reivaxy/celloAid/shell_3/20241109_110924.jpg

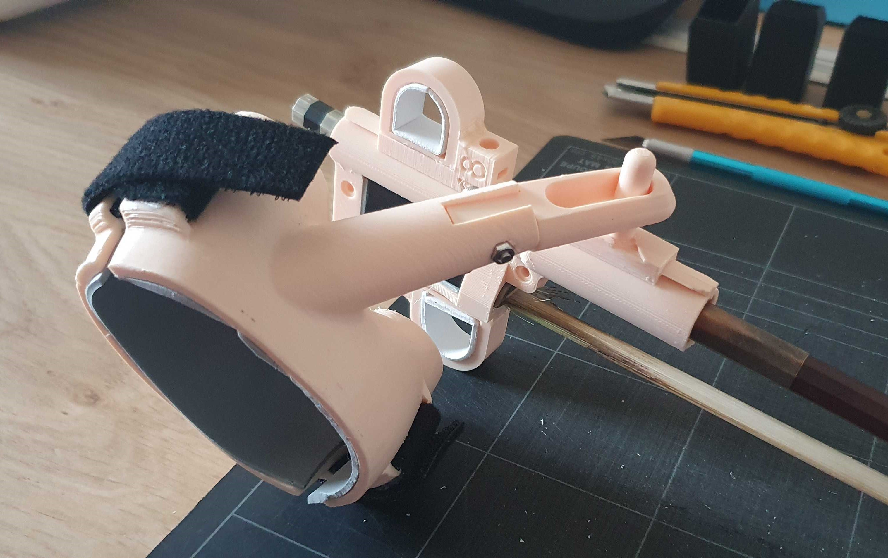
shell_3/20241109_110924.jpg
