reivaxy/celloAid/shell_3/20241109_110940.jpg

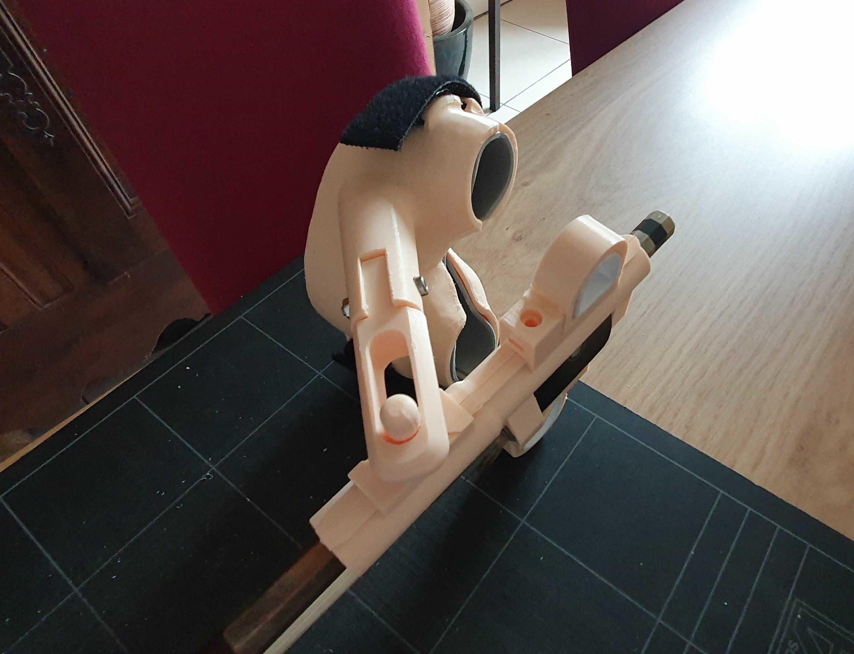
shell_3/20241109_110940.jpg
