reivaxy/celloAid/shell_3/20241109_110947.jpg

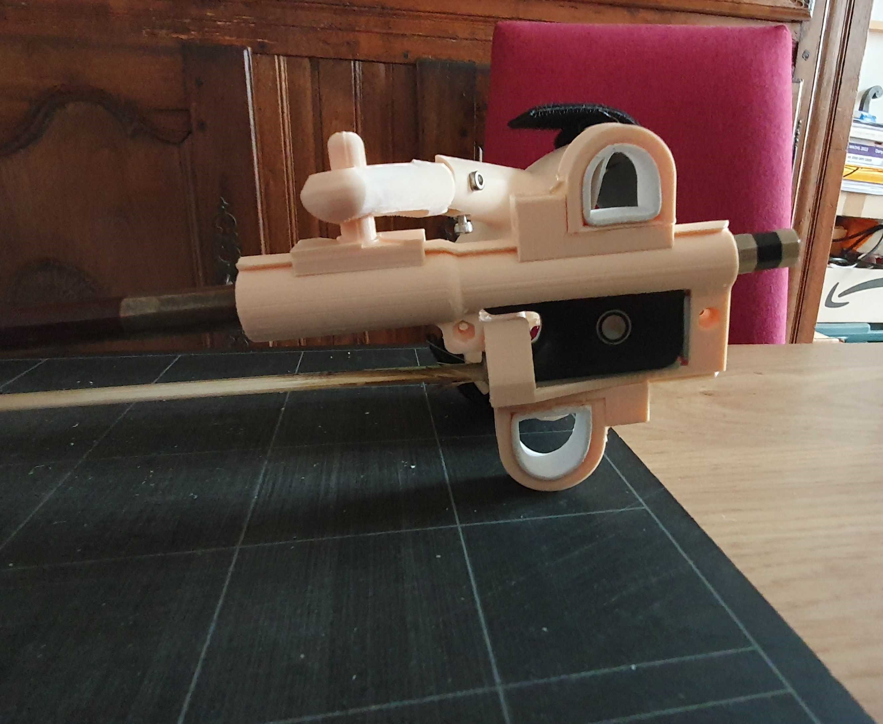
shell_3/20241109_110947.jpg
