reivaxy/celloAid/shell_3/index.stl

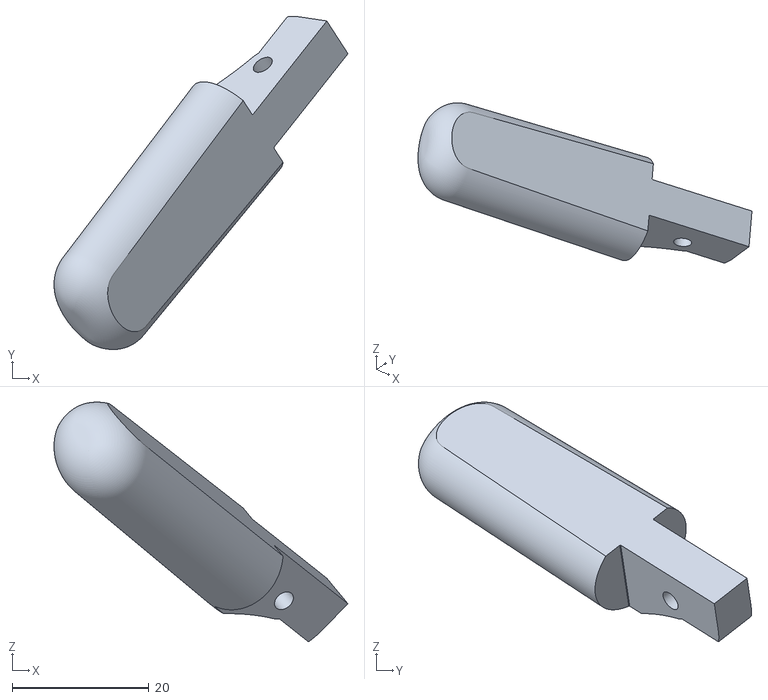
[picture p26: CAD file, 2024-11-09]
shell_3/index.stl
42.9 x 48.6 x 35.0
