reivaxy/celloAid/bow_1/hinge v2.stl

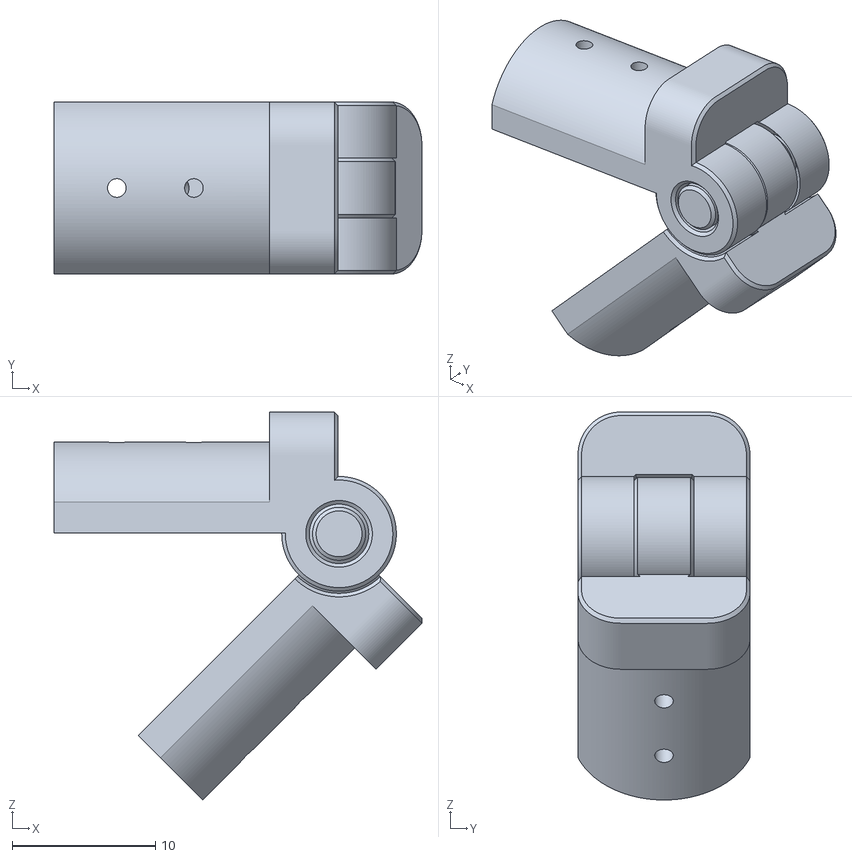
[picture p27: CAD file, 2024-08-30]
bow_1/hinge v2.stl
25.7 x 12.0 x 27.1
