reivaxy/celloAid/bow_2/lock.stl

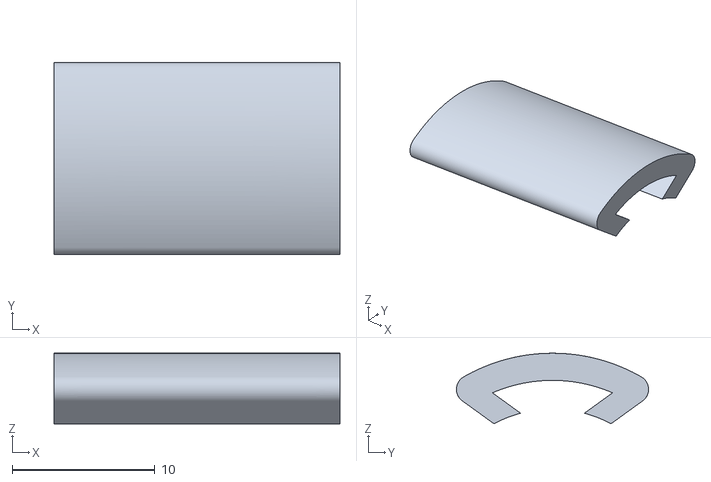
[picture p28: CAD file, 2024-08-30]
bow_2/lock.stl
20.0 x 13.4 x 4.93
