reivaxy/celloAid/bow_3/finger/circles/fingerRing.3mf

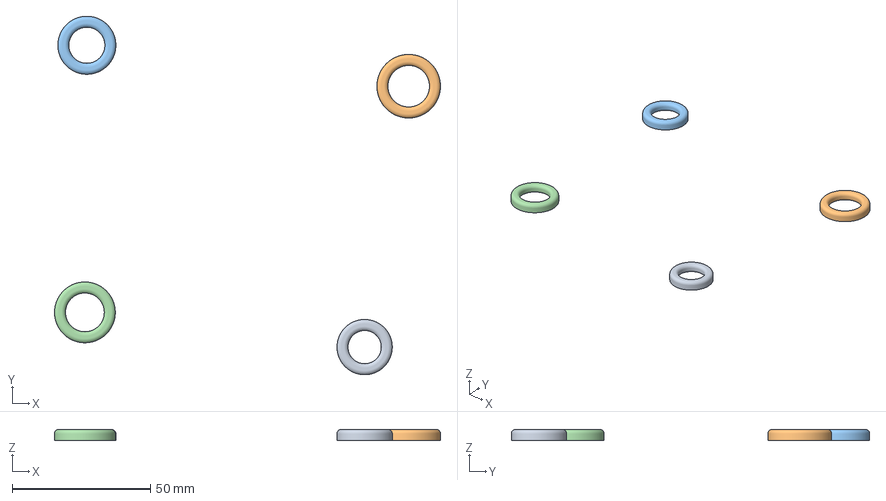
[picture p29: CAD file, 2024-09-11]
bow_3/finger/circles/fingerRing.3mf
139.6 x 129.7 x 4.00 mm
fingerRing12.stl
fingerRing15.stl
fingerRing13.stl
fingerRing14.stl
