reivaxy/celloAid/bow_3/finger/fingerSlider12.3mf

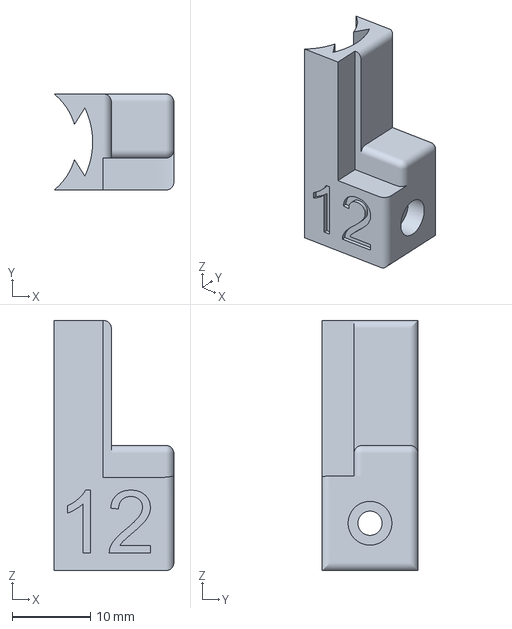
[picture p30: CAD file, 2024-10-21]
bow_3/finger/fingerSlider12.3mf
15.3 x 12.3 x 32.0 mm
