reivaxy/celloAid/bow_3/thumb/circles/thumbSlider20.3mf

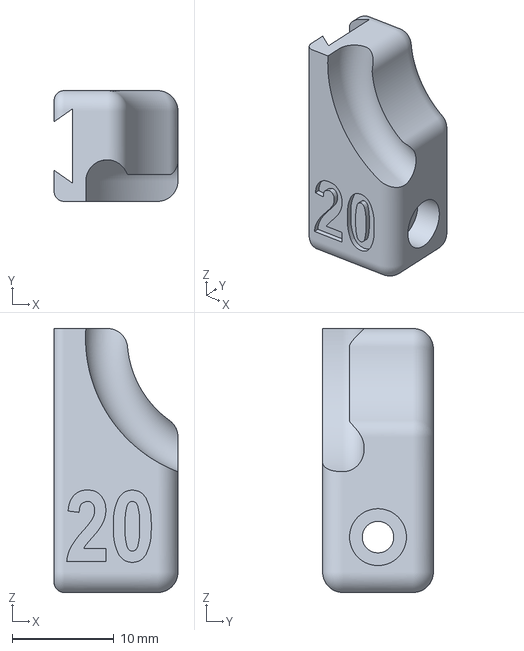
[picture p31: CAD file, 2024-09-11]
bow_3/thumb/circles/thumbSlider20.3mf
12.2 x 10.9 x 26.0 mm
