reivaxy/celloAid/bow_3/thumb/thumbRing16.3mf

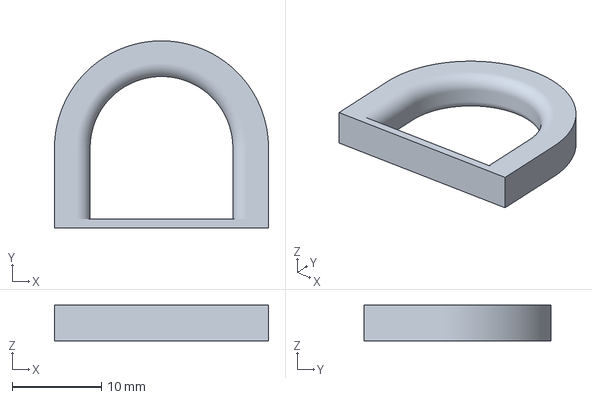
[picture p32: CAD file, 2024-10-21]
bow_3/thumb/thumbRing16.3mf
24.0 x 21.0 x 4.00 mm
