reivaxy/celloAid/bow_3/tubeRight.stl

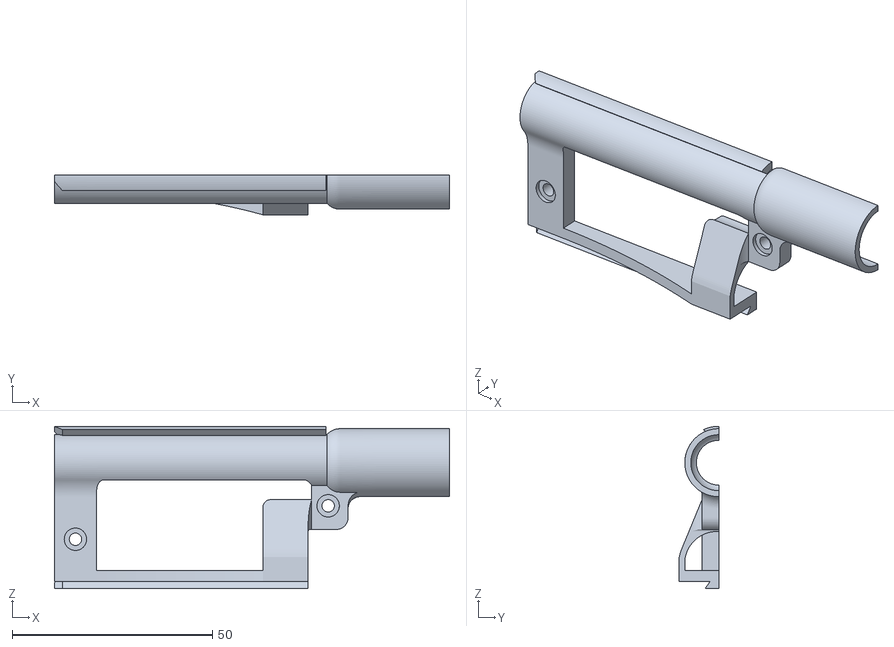
[picture p33: CAD file, 2024-08-30]
bow_3/tubeRight.stl
98.7 x 9.90 x 40.6
