reivaxy/celloAid/bow_4/indexRing5.stl

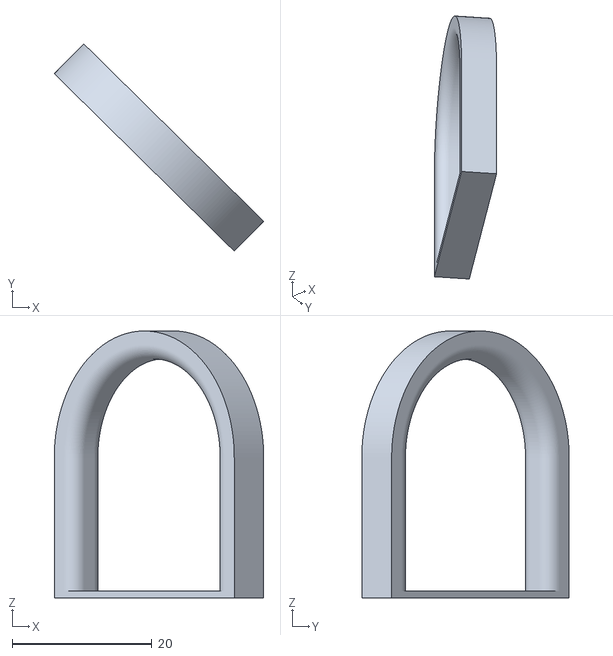
[picture p34: CAD file, 2024-11-09]
bow_4/indexRing5.stl
30.0 x 29.7 x 38.2
