reivaxy/celloAid/bow_5/bowBackHollower.stl

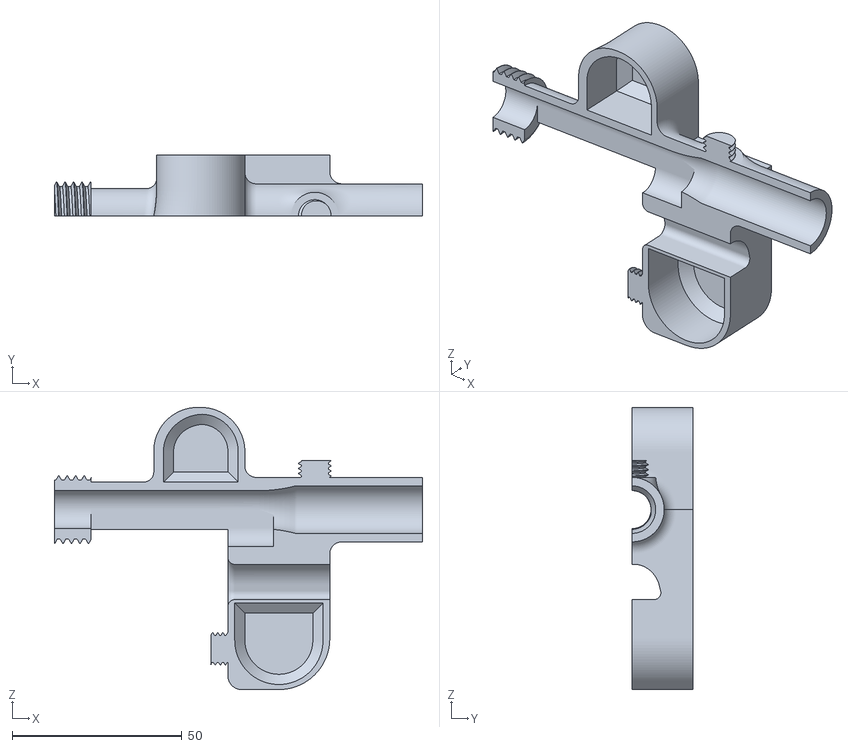
[picture p35: CAD file, 2024-11-27]
bow_5/bowBackHollower.stl
108.4 x 18.0 x 83.1
