reivaxy/celloAid/bow_7/front.stl

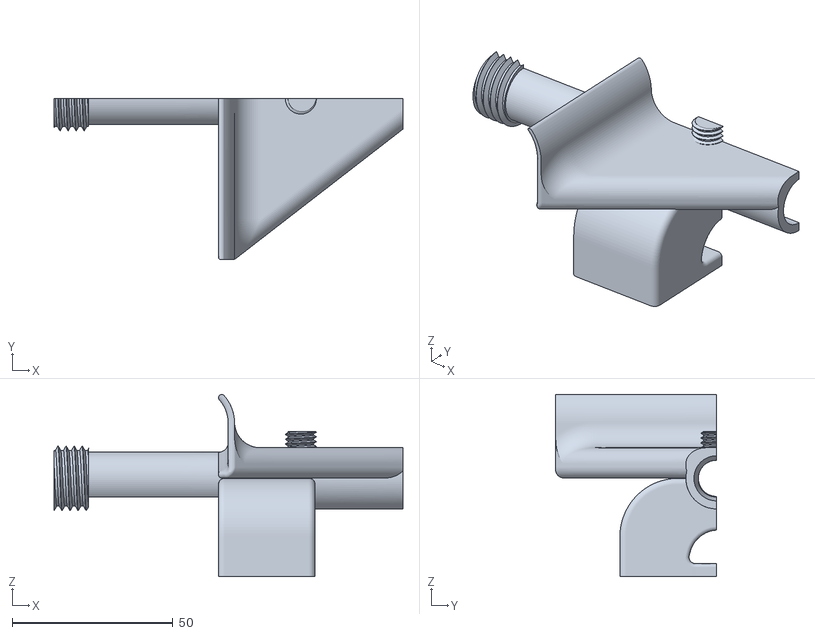
[picture p36: CAD file, 2025-01-11]
bow_7/front.stl
108.4 x 50.0 x 56.5
