reivaxy/celloAid/shell_1/tpuHinge.stl

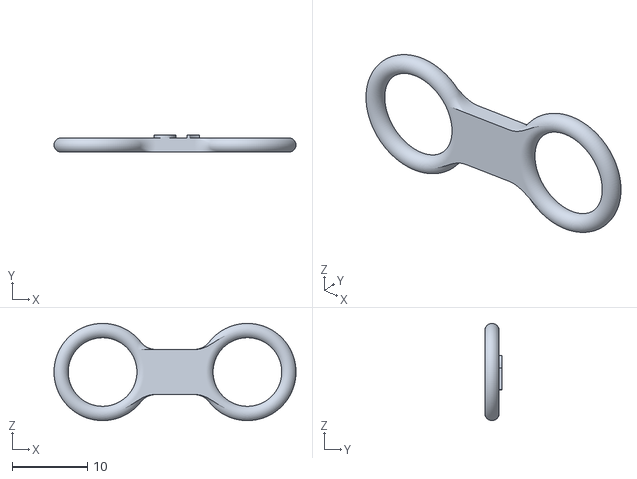
[picture p37: CAD file, 2024-08-30]
shell_1/tpuHinge.stl
32.1 x 2.30 x 12.9
