reivaxy/celloAid/shell_2/top.3mf

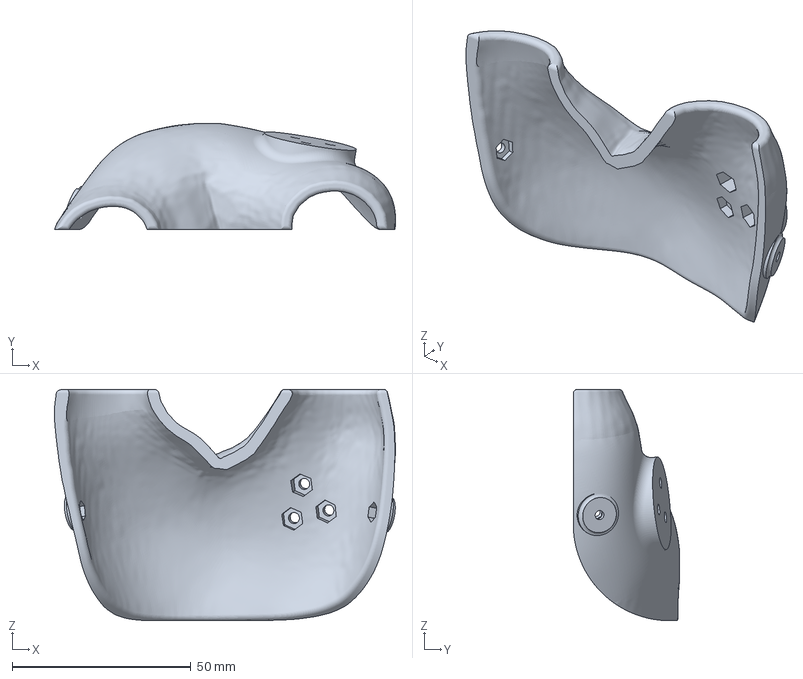
[picture p38: CAD file, 2024-10-21]
shell_2/top.3mf
95.5 x 29.8 x 64.8 mm
