reivaxy/celloAid/shell_3/indexWithSlot.stl

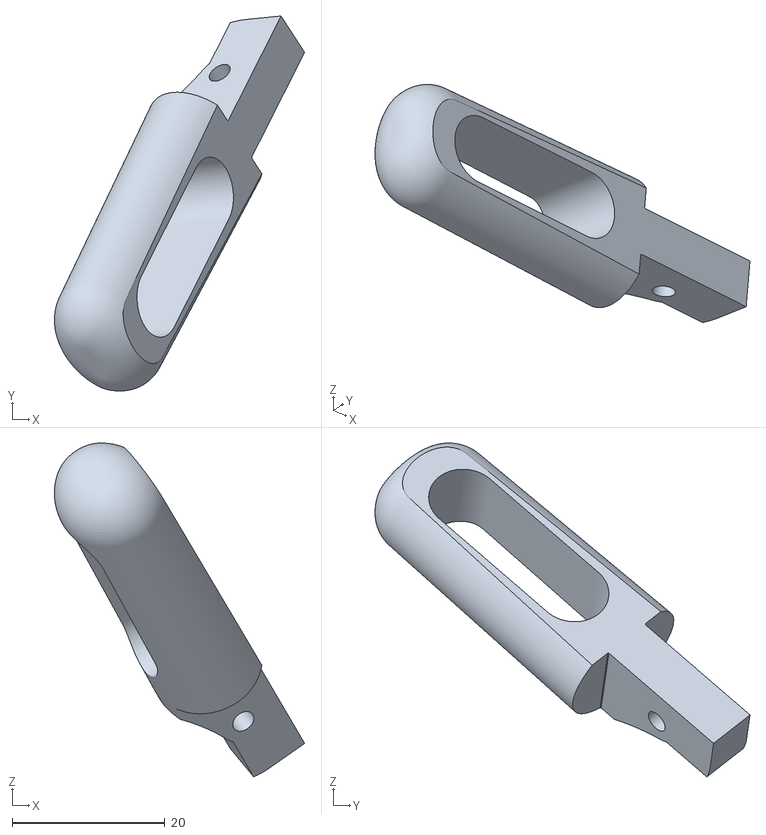
[picture p39: CAD file, 2024-11-09]
shell_3/indexWithSlot.stl
32.8 x 49.2 x 43.8
