reivaxy/celloAid/bow_1/testtubeRight.stl

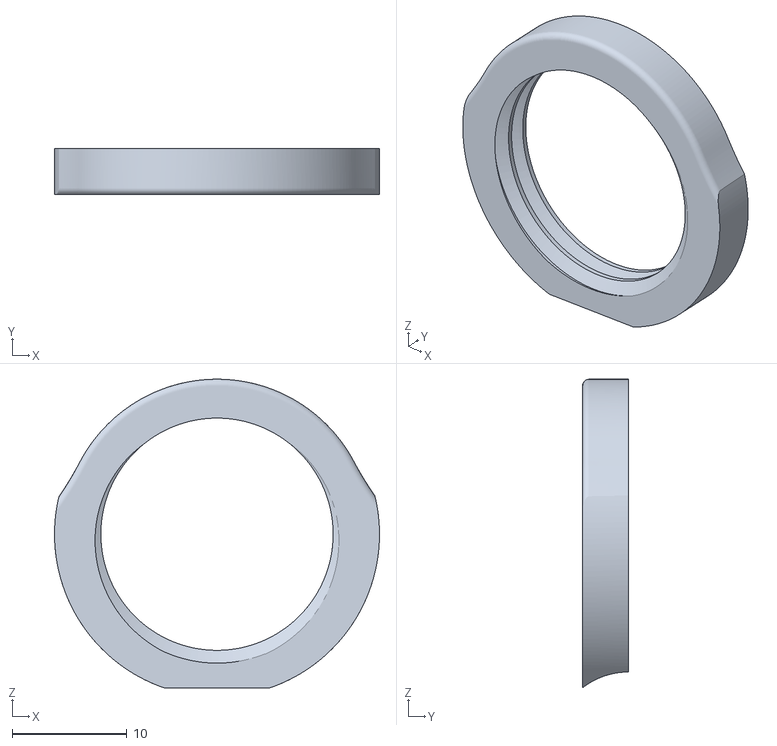
[picture p40: CAD file, 2024-08-30]
bow_1/testtubeRight.stl
28.3 x 4.01 x 26.9
