reivaxy/celloAid/bow_3/finger/circles/fingerSlider15.3mf

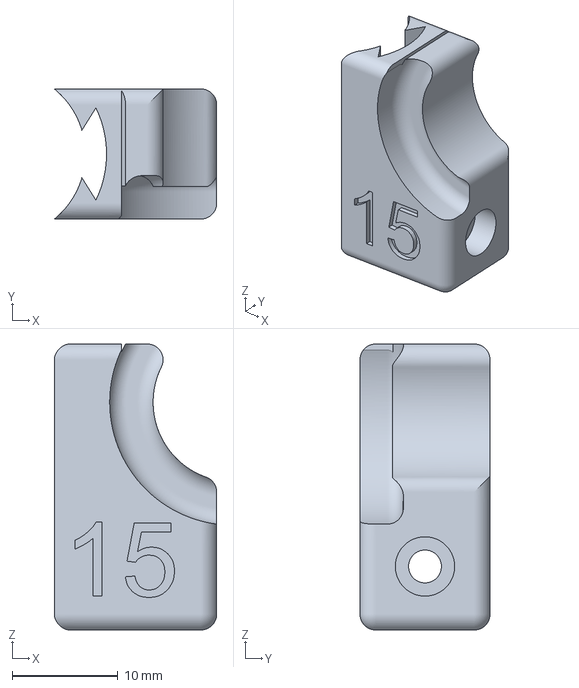
[picture p41: CAD file, 2024-09-11]
bow_3/finger/circles/fingerSlider15.3mf
15.3 x 12.3 x 27.0 mm
