reivaxy/celloAid/bow_3/finger/fingerSlider15.3mf

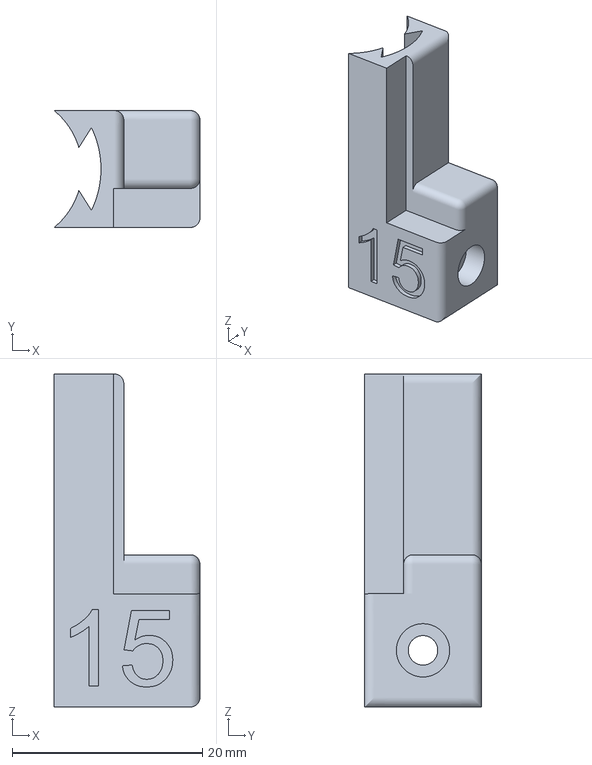
[picture p42: CAD file, 2024-10-21]
bow_3/finger/fingerSlider15.3mf
15.3 x 12.3 x 35.0 mm
