reivaxy/celloAid/bow_3/thumb/circles/thumbSlider17.3mf

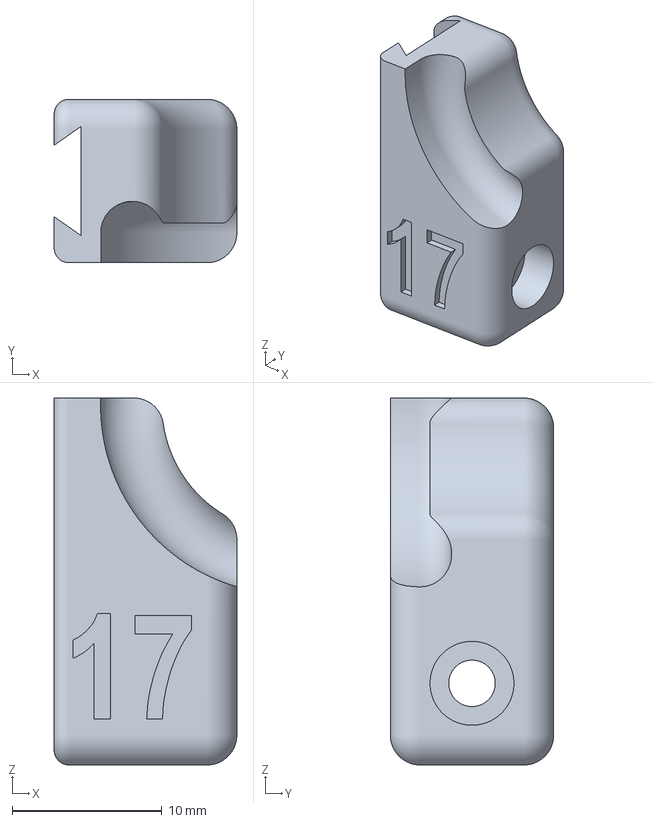
[picture p43: CAD file, 2024-09-11]
bow_3/thumb/circles/thumbSlider17.3mf
12.2 x 10.9 x 24.5 mm
