reivaxy/celloAid/bow_3/thumb/thumbRing17.3mf

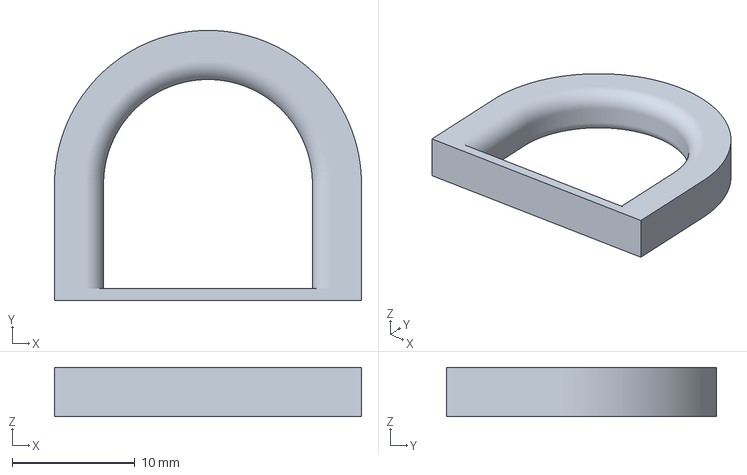
[picture p44: CAD file, 2024-10-21]
bow_3/thumb/thumbRing17.3mf
25.0 x 22.0 x 4.00 mm
