reivaxy/celloAid/bow_4/indexPivot.stl

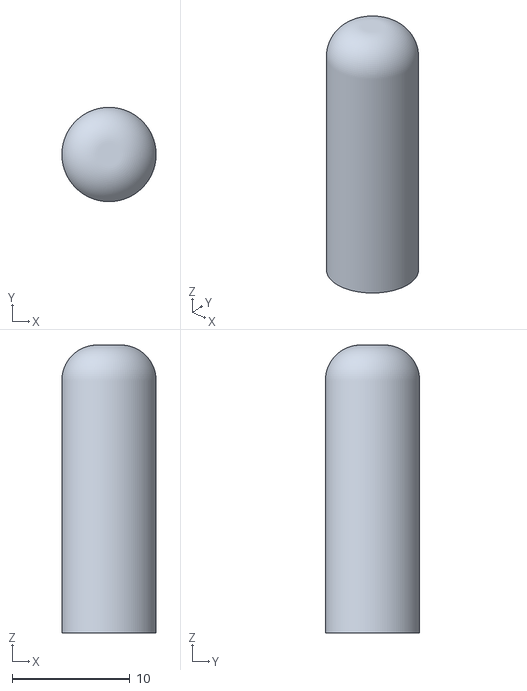
[picture p45: CAD file, 2024-11-09]
bow_4/indexPivot.stl
8.00 x 8.00 x 24.4
