reivaxy/celloAid/bow_5/bowBack.stl

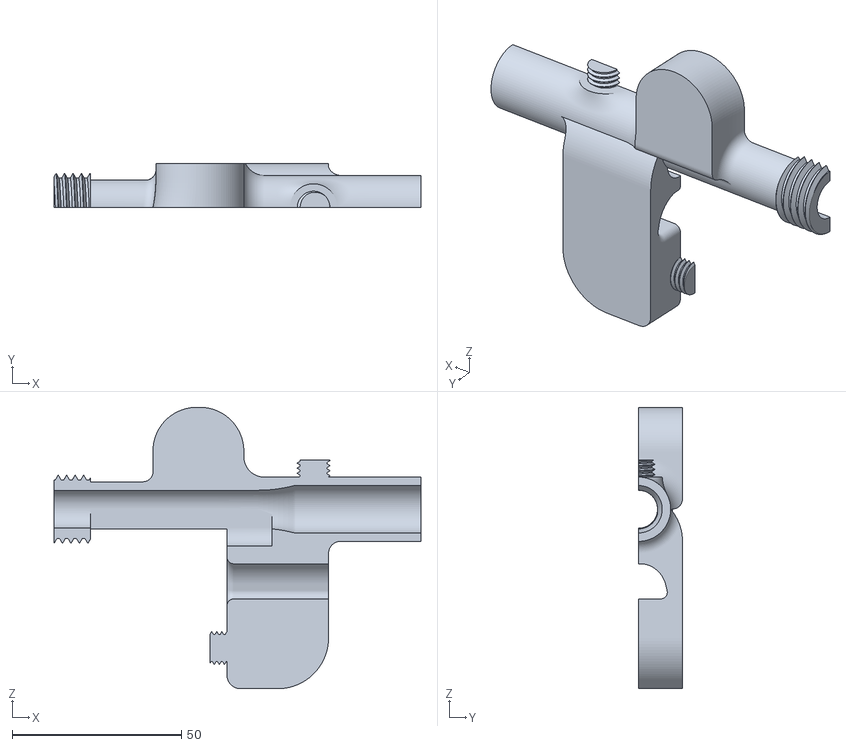
[picture p46: CAD file, 2024-11-24]
bow_5/bowBack.stl
108.4 x 13.0 x 83.1
