reivaxy/celloAid/bow_7/fakenut.stl

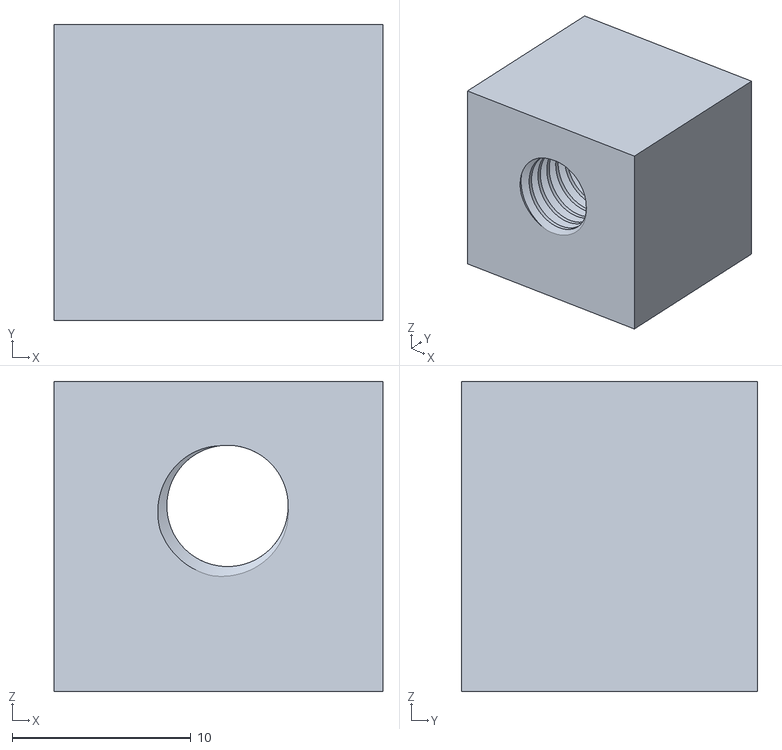
[picture p47: CAD file, 2025-01-11]
bow_7/fakenut.stl
18.4 x 16.5 x 17.3
