reivaxy/celloAid/shell_1/outer (7).stl

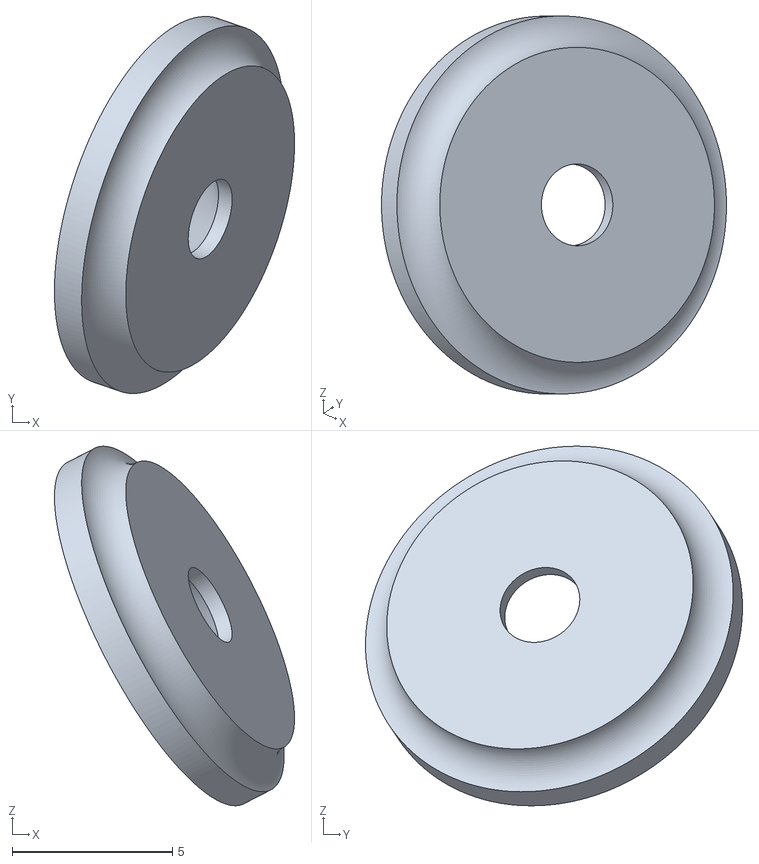
[picture p48: CAD file, 2024-08-30]
shell_1/outer (7).stl
7.49 x 11.8 x 11.2
