reivaxy/celloAid/bow_2/hinge v2.stl

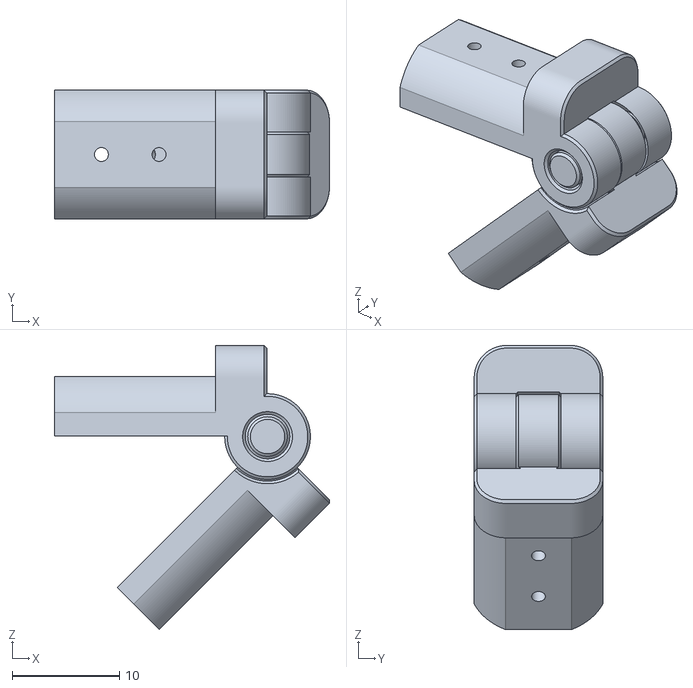
[picture p49: CAD file, 2024-08-30]
bow_2/hinge v2.stl
25.7 x 12.0 x 26.5
