reivaxy/celloAid/bow_3/finger/circles/fingerSlider12.3mf

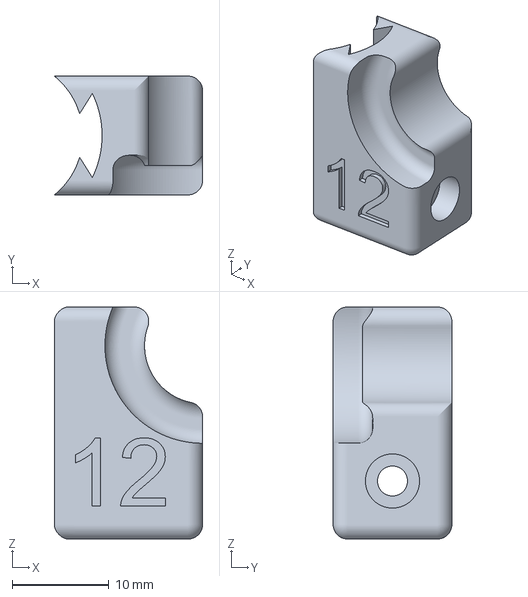
[picture p50: CAD file, 2024-09-11]
bow_3/finger/circles/fingerSlider12.3mf
15.3 x 12.3 x 24.0 mm
