reivaxy/celloAid/bow_3/finger/fingerRing14.stl

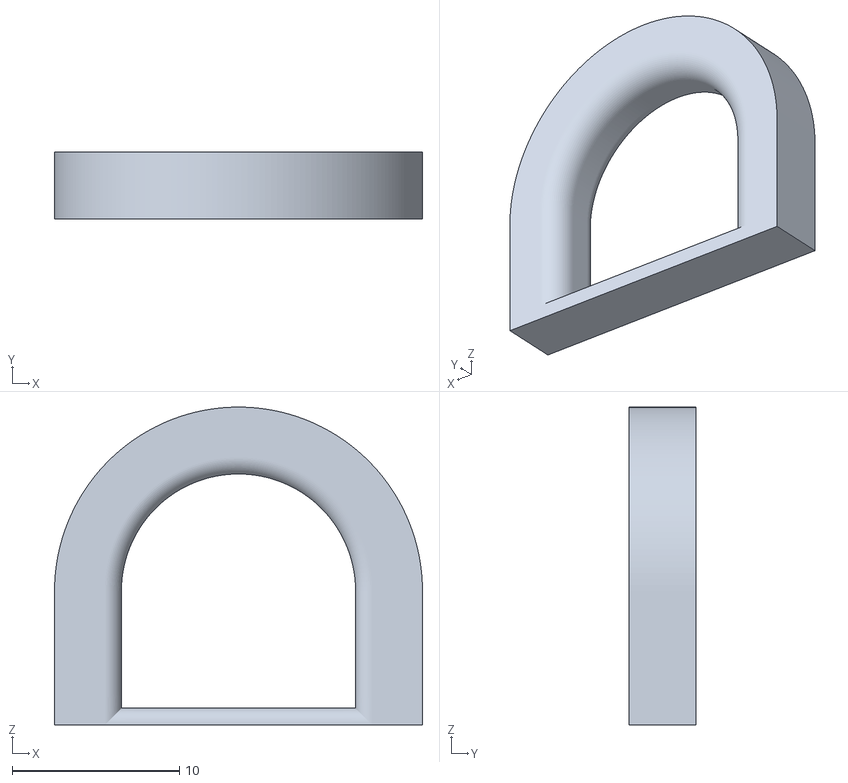
[picture p51: CAD file, 2024-10-21]
bow_3/finger/fingerRing14.stl
22.0 x 4.00 x 19.0
