reivaxy/celloAid/bow_3/thumb/circles/thumbSlider18.3mf

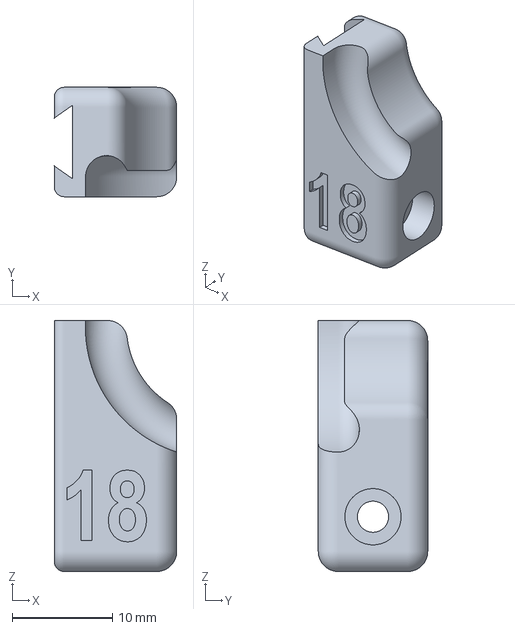
[picture p52: CAD file, 2024-09-11]
bow_3/thumb/circles/thumbSlider18.3mf
12.2 x 10.9 x 25.0 mm
