reivaxy/celloAid/bow_3/thumb/thumbSlider16.3mf

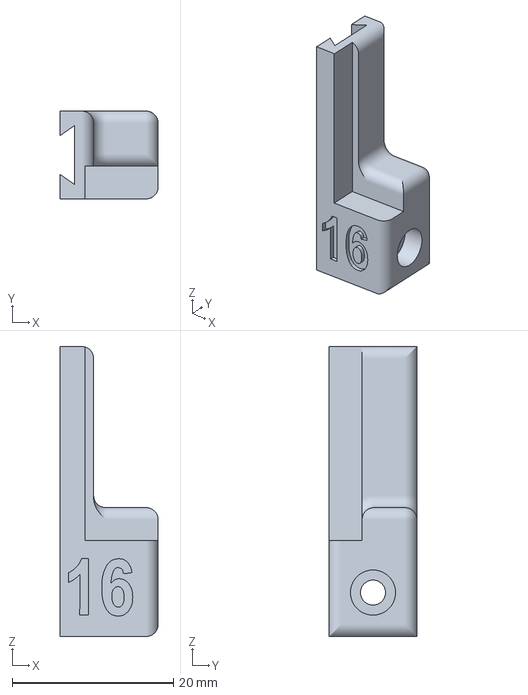
[picture p53: CAD file, 2024-10-21]
bow_3/thumb/thumbSlider16.3mf
12.2 x 10.9 x 36.0 mm
