reivaxy/celloAid/bow_4/indexRing4.stl

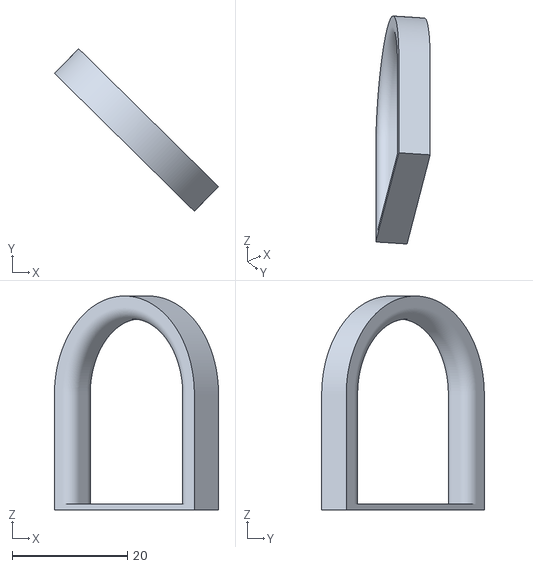
[picture p54: CAD file, 2024-11-09]
bow_4/indexRing4.stl
28.5 x 28.3 x 37.2
