reivaxy/celloAid/bow_5/bowFront.stl

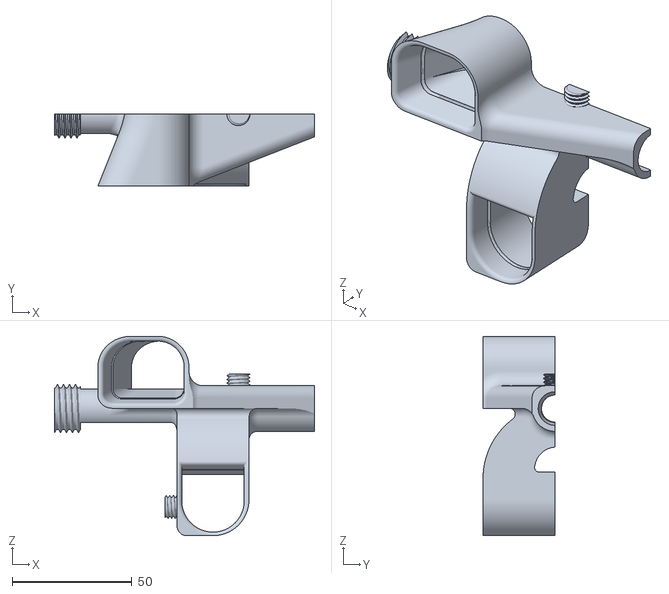
[picture p55: CAD file, 2024-11-24]
bow_5/bowFront.stl
108.4 x 30.0 x 83.1
