reivaxy/celloAid/bow_7/back.stl

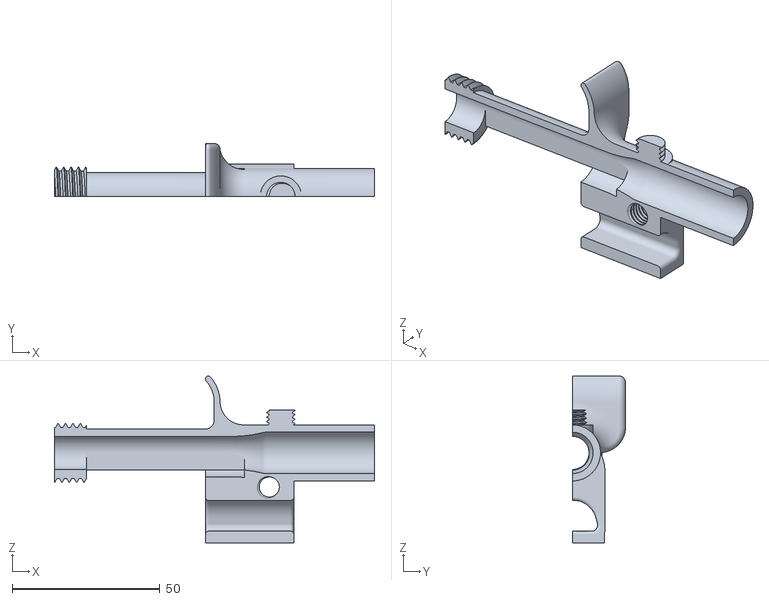
[picture p56: CAD file, 2025-01-11]
bow_7/back.stl
108.4 x 18.0 x 56.5
