reivaxy/celloAid/shell_1/tpuHook.stl

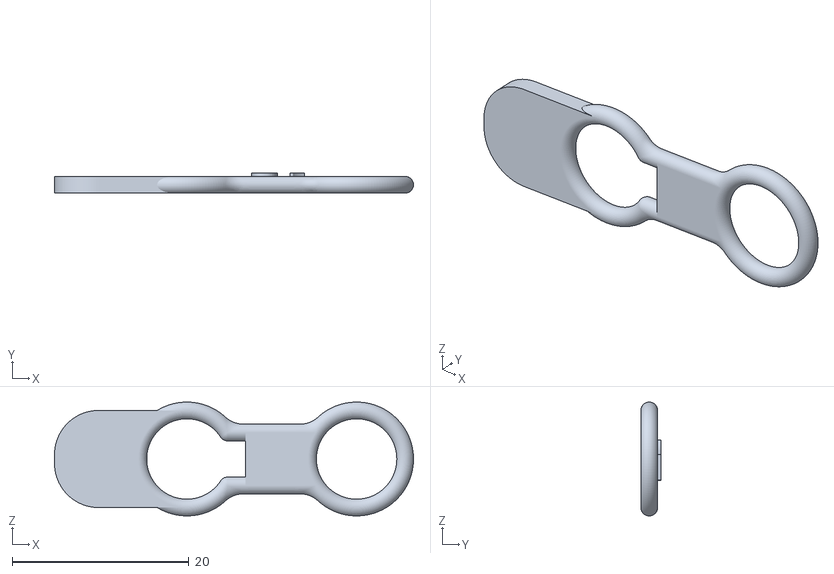
[picture p57: CAD file, 2024-08-30]
shell_1/tpuHook.stl
40.7 x 2.30 x 12.9
