reivaxy/celloAid/bow_1/testBigtubeRight.stl

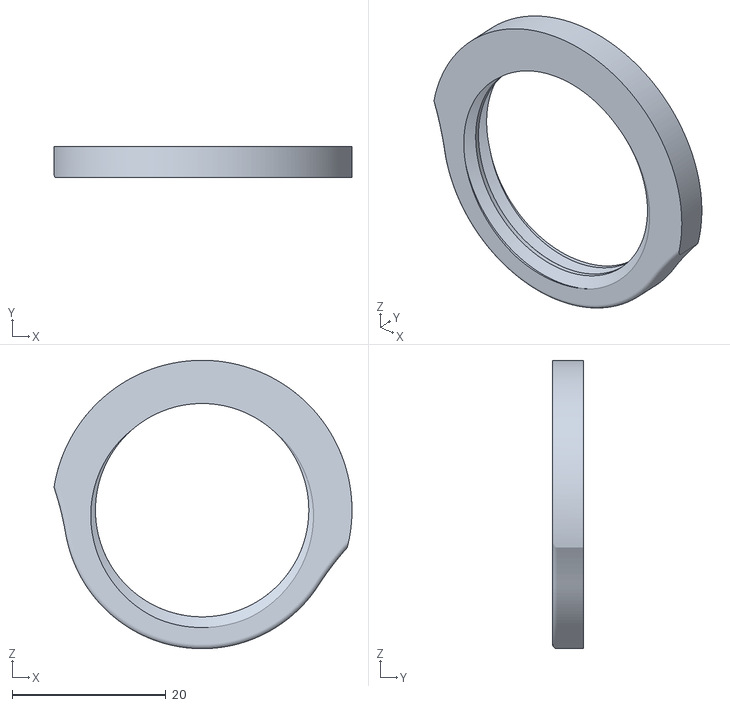
[picture p58: CAD file, 2024-08-30]
bow_1/testBigtubeRight.stl
38.7 x 4.01 x 37.5
