reivaxy/celloAid/bow_3/finger/circles/fingerSlider14.3mf

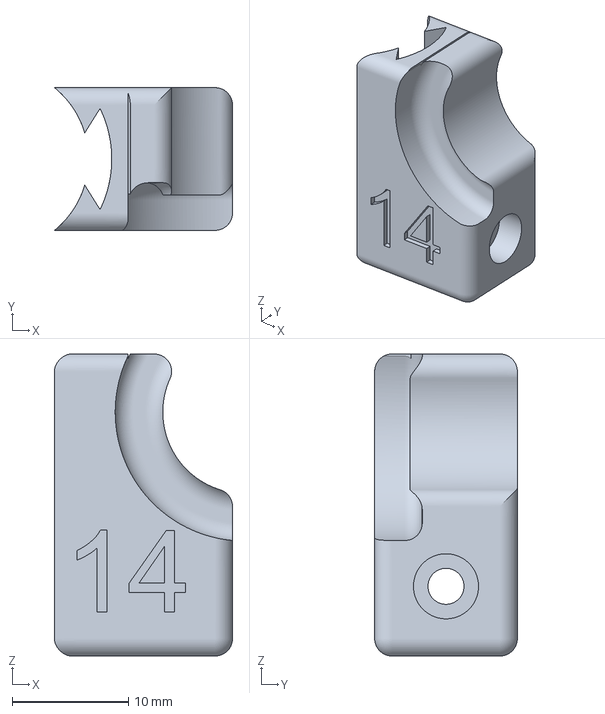
[picture p59: CAD file, 2024-09-11]
bow_3/finger/circles/fingerSlider14.3mf
15.3 x 12.3 x 26.0 mm
