reivaxy/celloAid/bow_3/finger/fingerRing15.stl

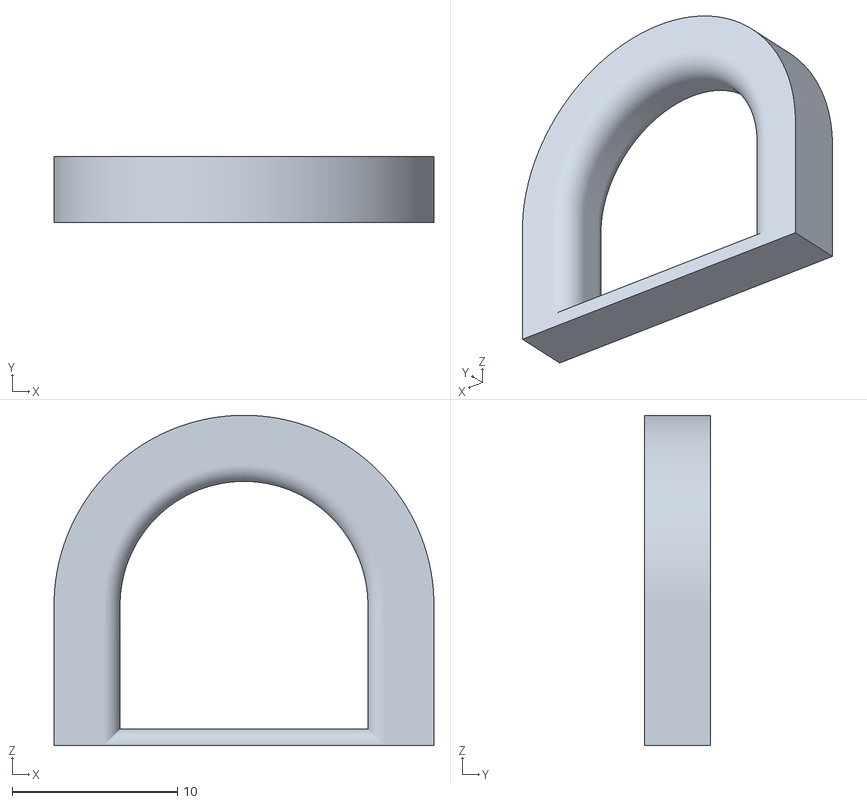
[picture p60: CAD file, 2024-10-21]
bow_3/finger/fingerRing15.stl
23.0 x 4.00 x 20.0
