reivaxy/celloAid/bow_3/thumb/thumbRing20.3mf

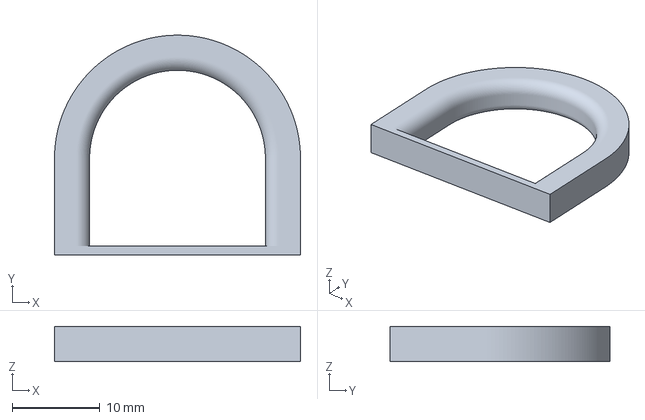
[picture p61: CAD file, 2024-10-21]
bow_3/thumb/thumbRing20.3mf
28.0 x 25.0 x 4.00 mm
