reivaxy/celloAid/bow_4/tubeRight.stl

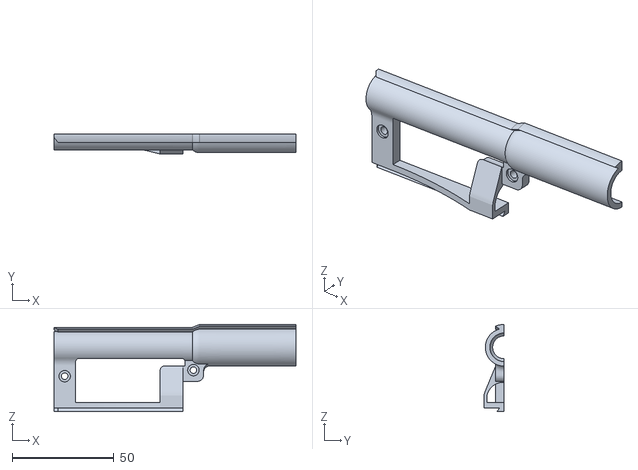
[picture p62: CAD file, 2024-11-09]
bow_4/tubeRight.stl
118.7 x 9.90 x 42.7
