reivaxy/celloAid/shell_1/outerTopLeftWrist.stl

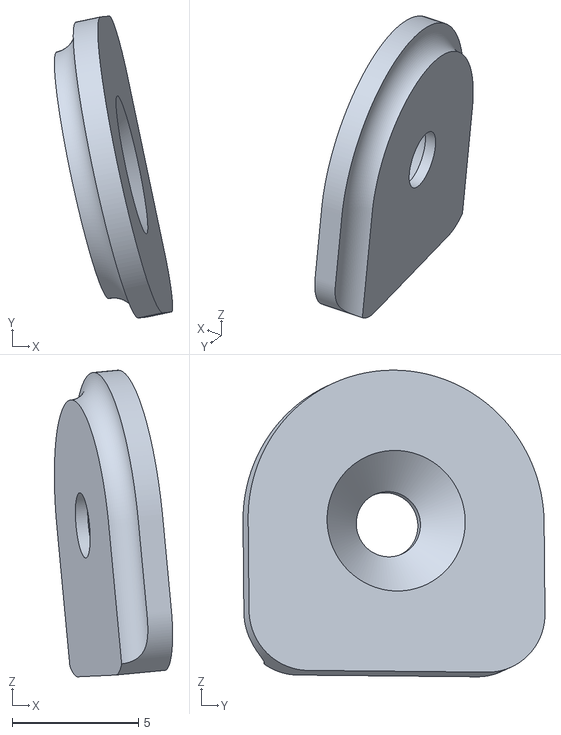
[picture p63: CAD file, 2024-08-30]
shell_1/outerTopLeftWrist.stl
4.69 x 12.0 x 12.2
