reivaxy/celloAid/bow_3/finger/circles/fingerRing13.stl

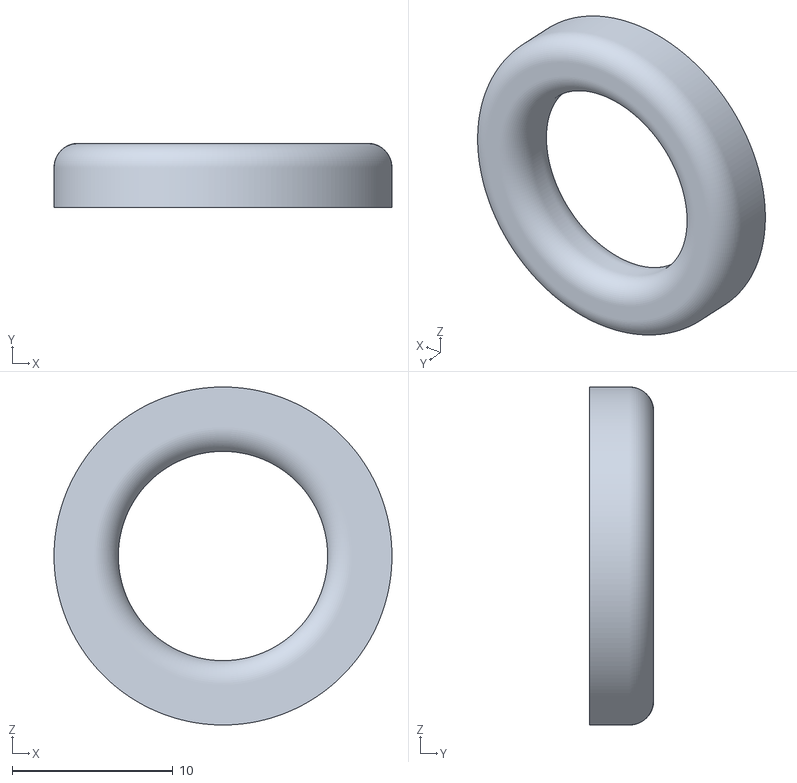
[picture p64: CAD file, 2024-08-30]
bow_3/finger/circles/fingerRing13.stl
21.0 x 4.00 x 21.0
