reivaxy/celloAid/bow_3/finger/fingerSlider14.3mf

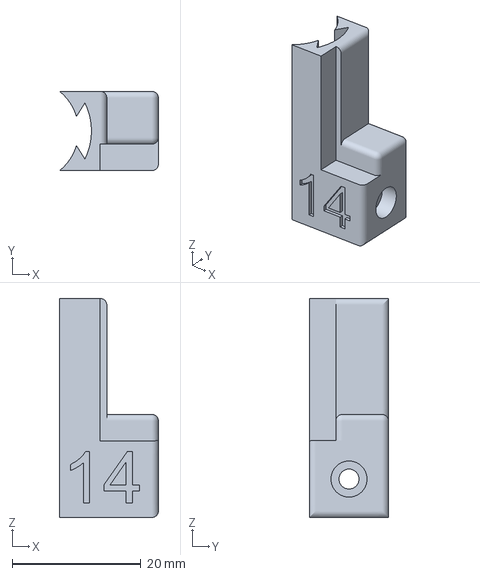
[picture p65: CAD file, 2024-10-21]
bow_3/finger/fingerSlider14.3mf
15.3 x 12.3 x 34.0 mm
