reivaxy/celloAid/bow_3/thumb/thumbSlider19.3mf

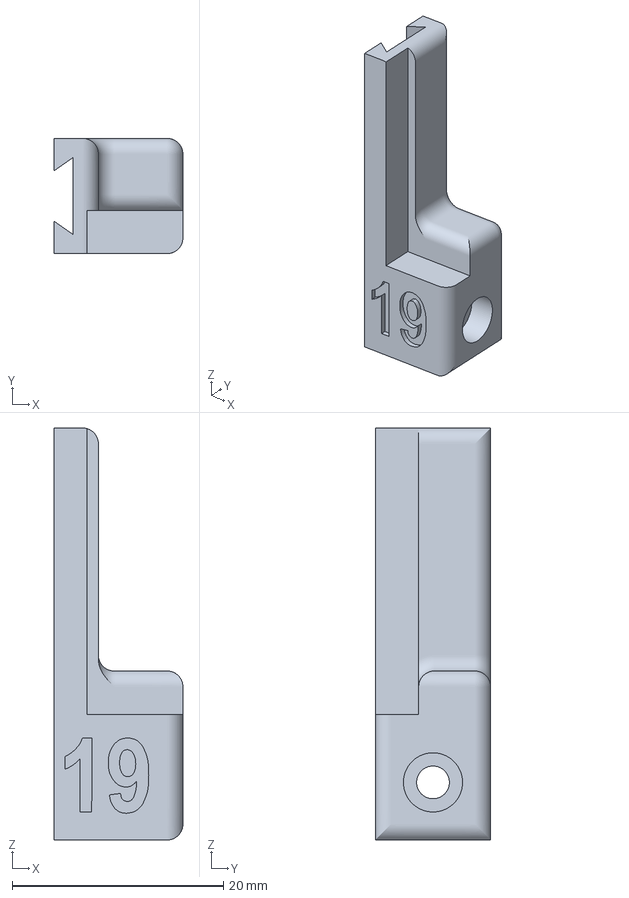
[picture p66: CAD file, 2024-10-21]
bow_3/thumb/thumbSlider19.3mf
12.2 x 10.9 x 39.0 mm
