reivaxy/celloAid/bow_4/thumbRing21.stl

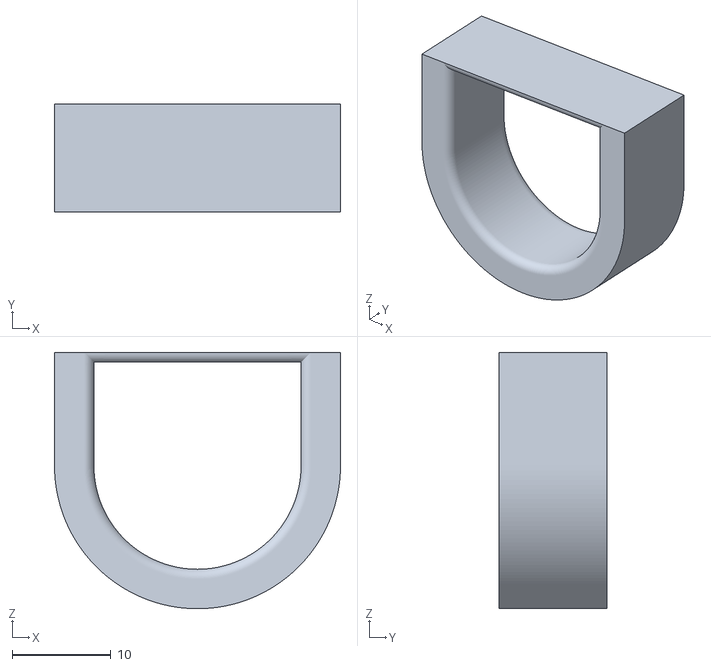
[picture p67: CAD file, 2024-11-09]
bow_4/thumbRing21.stl
29.0 x 10.9 x 26.0
