reivaxy/celloAid/bow_3/finger/circles/fingerRing15.stl

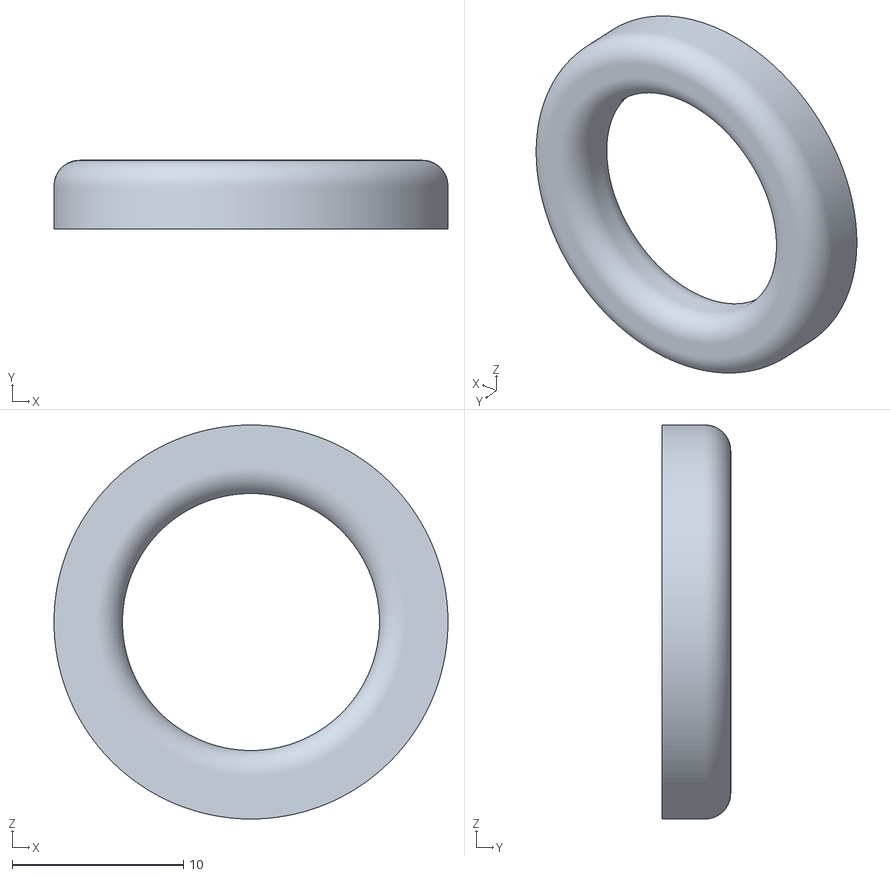
[picture p68: CAD file, 2024-08-30]
bow_3/finger/circles/fingerRing15.stl
23.0 x 4.00 x 23.0
