reivaxy/celloAid/bow_3/finger/fingerSlider16.3mf

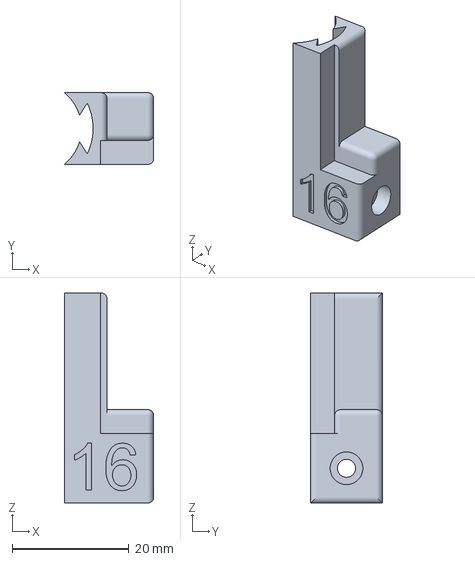
[picture p69: CAD file, 2024-10-21]
bow_3/finger/fingerSlider16.3mf
15.3 x 12.3 x 36.0 mm
