reivaxy/celloAid/bow_3/thumb/thumbRing19.3mf

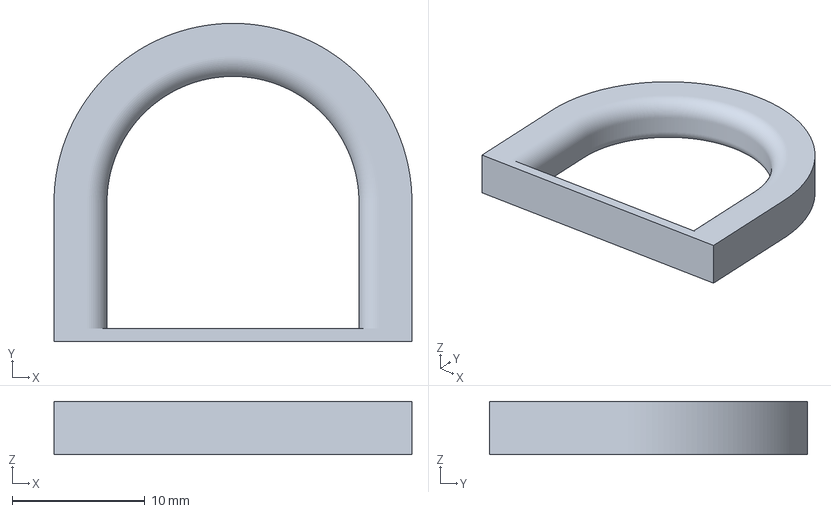
[picture p71: CAD file, 2024-10-21]
bow_3/thumb/thumbRing19.3mf
27.0 x 24.0 x 4.00 mm
