reivaxy/celloAid/bow_4/fingerRing18.stl

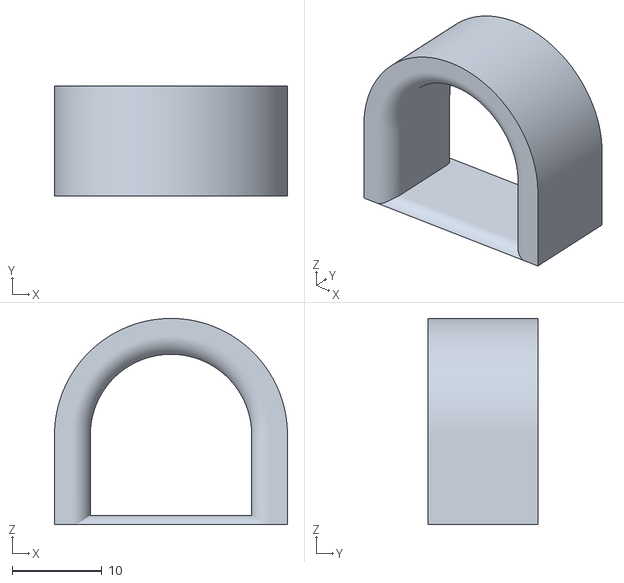
[picture p72: CAD file, 2024-11-09]
bow_4/fingerRing18.stl
26.0 x 12.3 x 23.0
