reivaxy/celloAid/bow_3/finger/circles/fingerRing12.stl

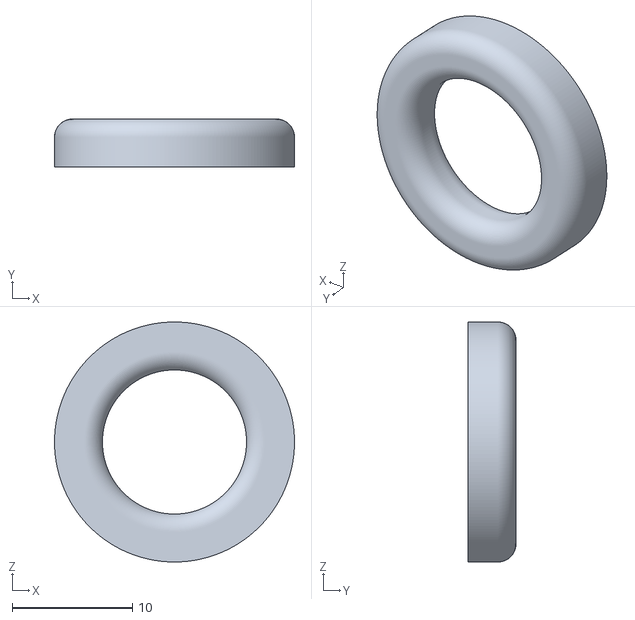
[picture p73: CAD file, 2024-08-30]
bow_3/finger/circles/fingerRing12.stl
20.0 x 4.00 x 20.0
