reivaxy/celloAid/bow_3/finger/fingerRings.3mf

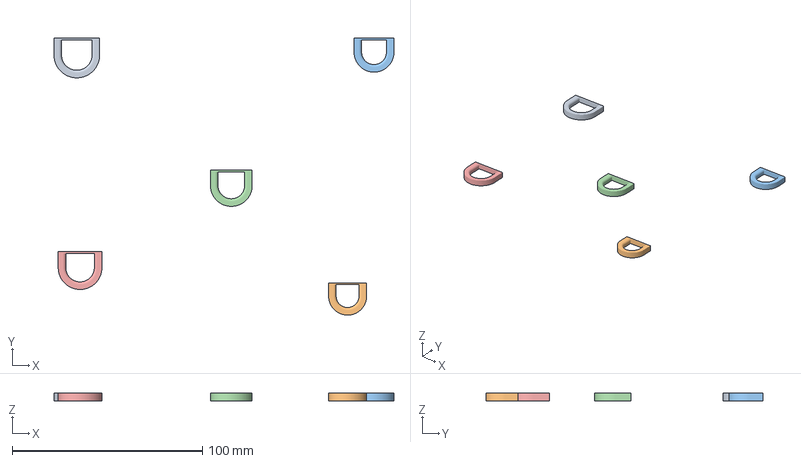
[picture p74: CAD file, 2024-10-21]
bow_3/finger/fingerRings.3mf
178.8 x 145.7 x 4.00 mm
fingerRing16.stl
fingerRing12.stl
fingerRing13.stl
fingerRing14.stl
fingerRing15.stl
