reivaxy/celloAid/bow_3/thumb/circles/thumbSlider22.3mf

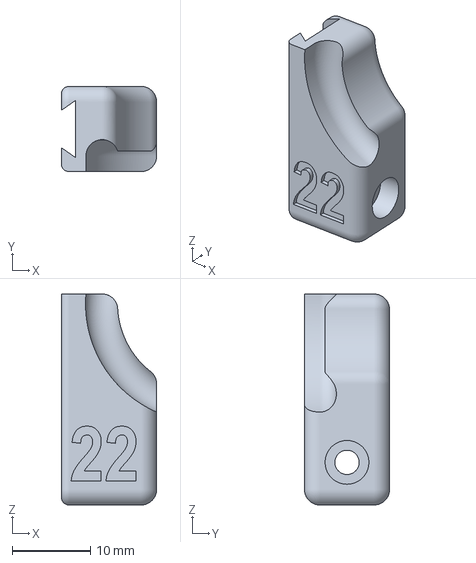
[picture p75: CAD file, 2024-09-11]
bow_3/thumb/circles/thumbSlider22.3mf
12.2 x 10.9 x 27.0 mm
