reivaxy/celloAid/bow_3/thumb/thumbSlider20.3mf

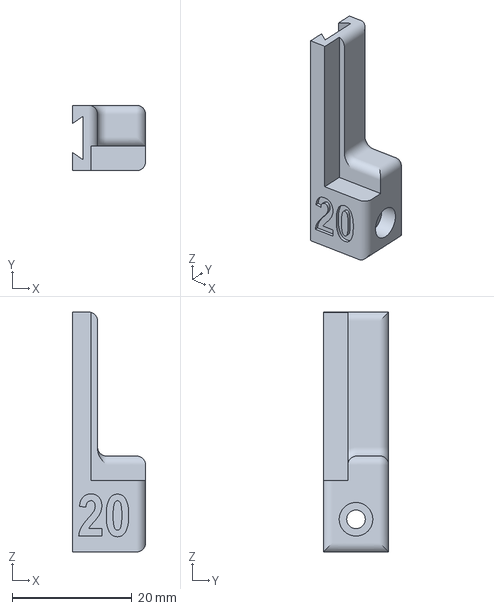
[picture p76: CAD file, 2024-10-21]
bow_3/thumb/thumbSlider20.3mf
12.2 x 10.9 x 40.0 mm
