reivaxy/celloAid/bow_4/indexRing3.stl

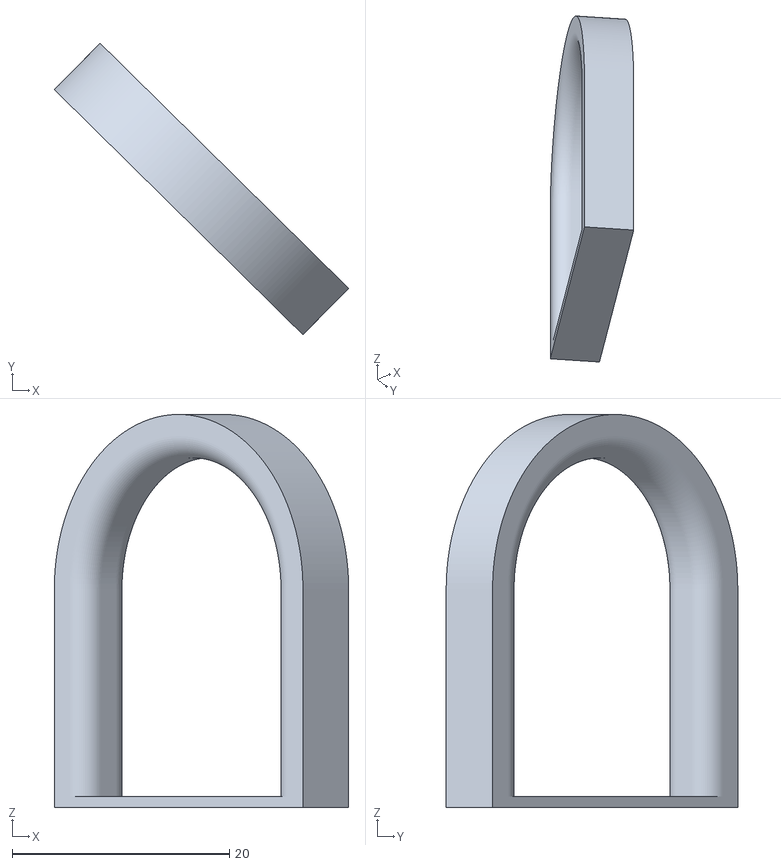
[picture p77: CAD file, 2024-11-09]
bow_4/indexRing3.stl
27.1 x 26.9 x 36.2
