reivaxy/celloAid/bow_3/finger/circles/fingerRing14.stl

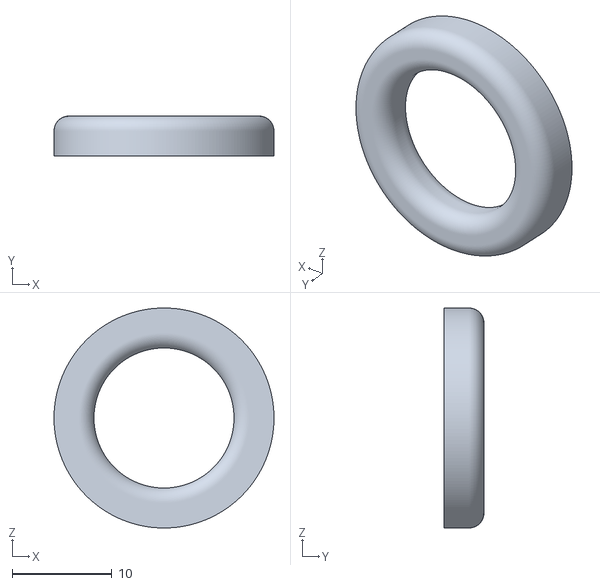
[picture p78: CAD file, 2024-08-30]
bow_3/finger/circles/fingerRing14.stl
22.0 x 4.00 x 22.0
