reivaxy/celloAid/bow_3/thumb/circles/thumbRing19.stl

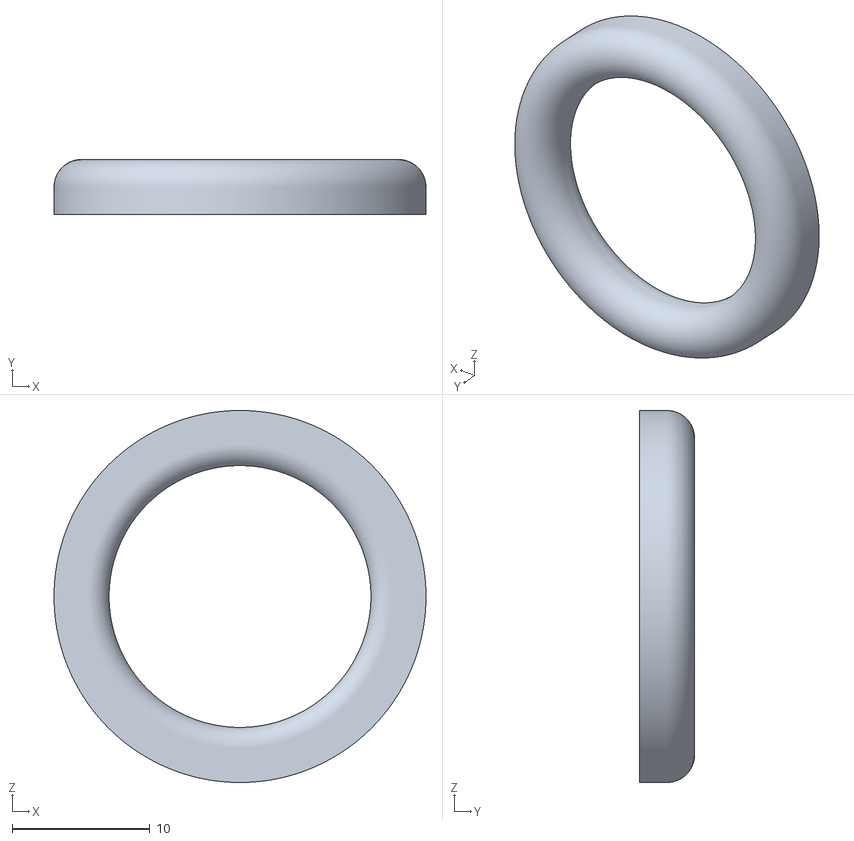
[picture p79: CAD file, 2024-08-30]
bow_3/thumb/circles/thumbRing19.stl
27.0 x 4.00 x 27.0
