reivaxy/celloAid/bow_3/thumb/thumbSlider18.3mf

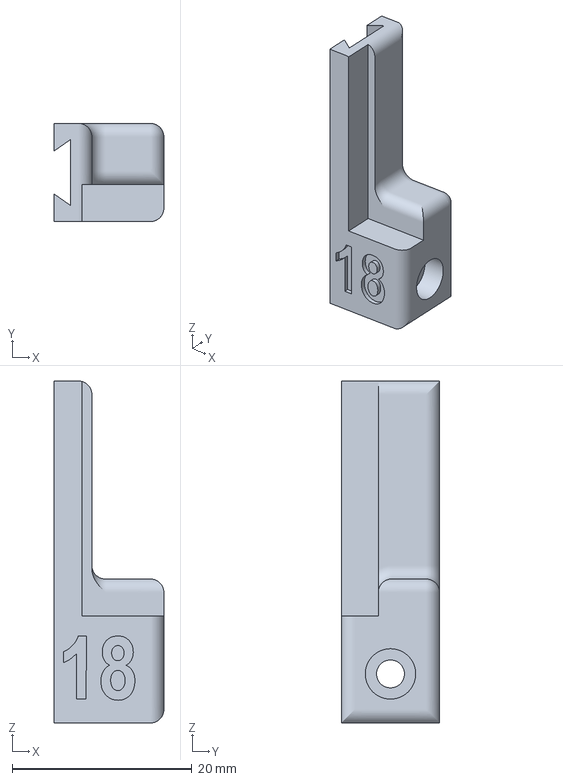
[picture p80: CAD file, 2024-10-21]
bow_3/thumb/thumbSlider18.3mf
12.2 x 10.9 x 38.0 mm
