reivaxy/celloAid/bow_3/finger/fingerRing12.stl

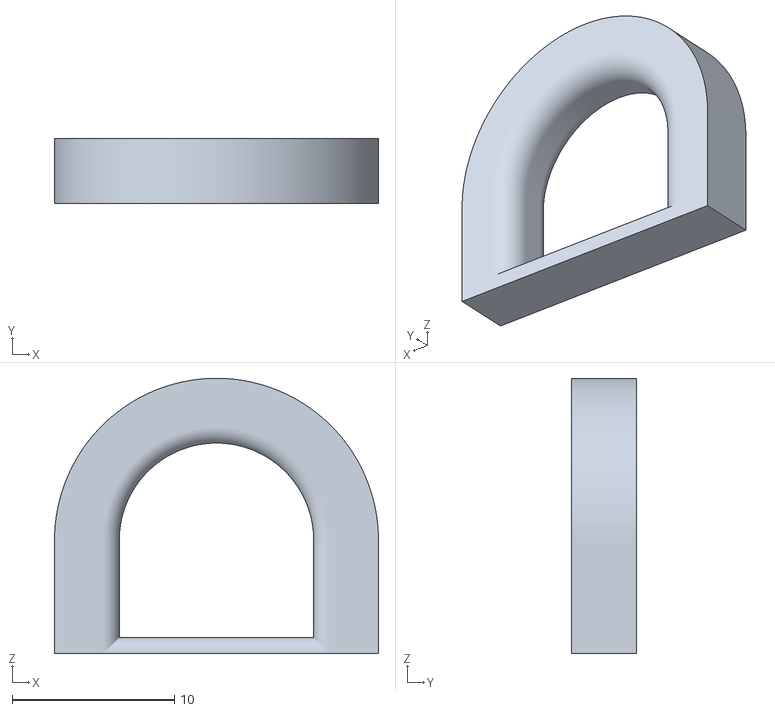
[picture p81: CAD file, 2024-10-21]
bow_3/finger/fingerRing12.stl
20.0 x 4.00 x 17.0
