reivaxy/celloAid/bow_3/thumb/circles/thumbRing18.stl

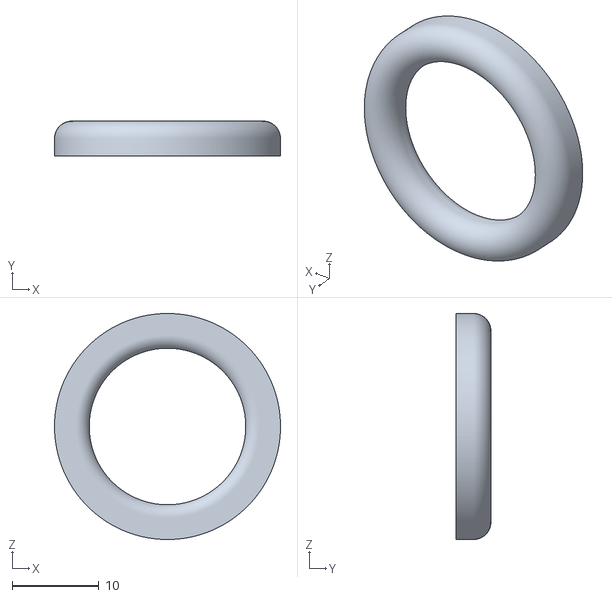
[picture p82: CAD file, 2024-08-30]
bow_3/thumb/circles/thumbRing18.stl
26.0 x 4.00 x 26.0
