reivaxy/celloAid/bow_3/thumb/thumbRing21.3mf

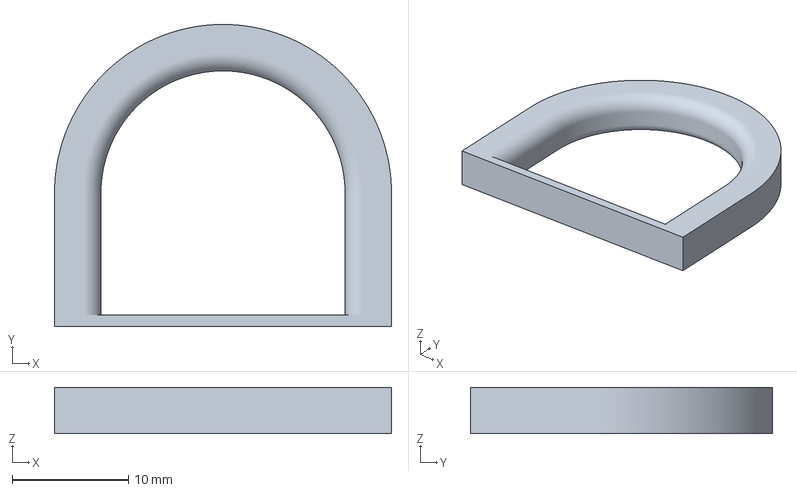
[picture p83: CAD file, 2024-10-21]
bow_3/thumb/thumbRing21.3mf
29.0 x 26.0 x 4.00 mm
