reivaxy/celloAid/bow_4/indexSlider.stl

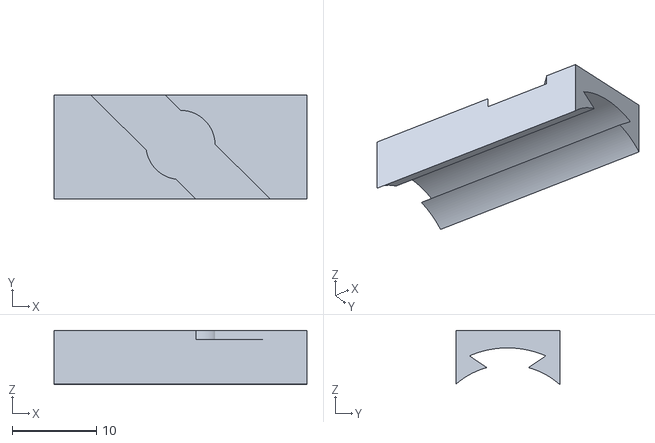
[picture p84: CAD file, 2024-11-09]
bow_4/indexSlider.stl
30.0 x 12.3 x 6.43
