reivaxy/celloAid/bow_3/finger/fingerRing13.stl

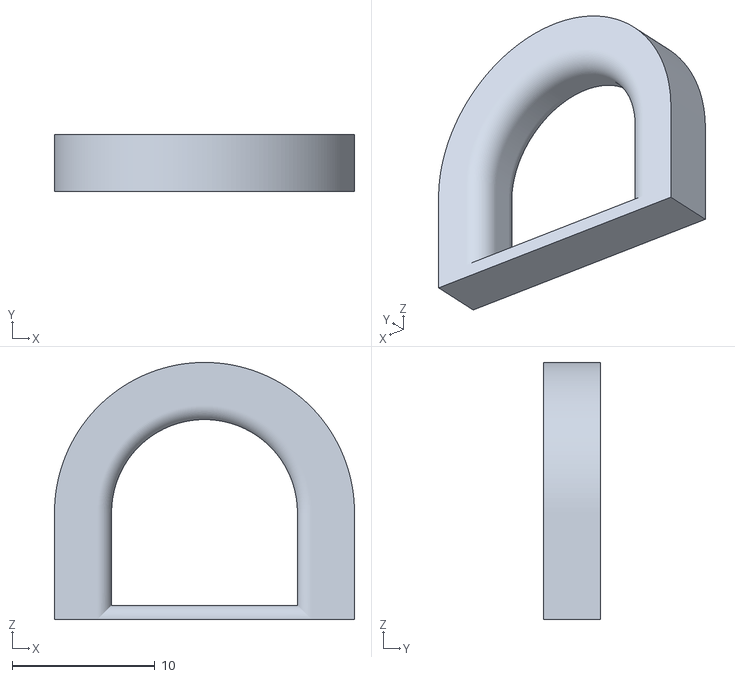
[picture p85: CAD file, 2024-10-21]
bow_3/finger/fingerRing13.stl
21.0 x 4.00 x 18.0
