reivaxy/celloAid/bow_3/thumb/circles/thumbRing22.stl

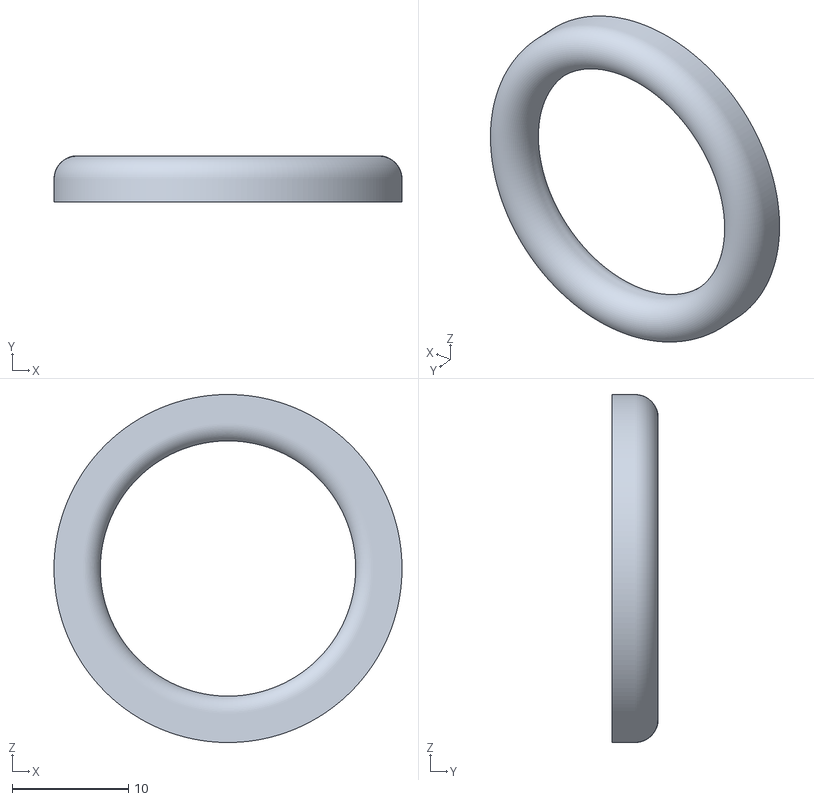
[picture p86: CAD file, 2024-08-30]
bow_3/thumb/circles/thumbRing22.stl
30.0 x 4.00 x 30.0
