reivaxy/celloAid/bow_4/fingerSlider18.stl

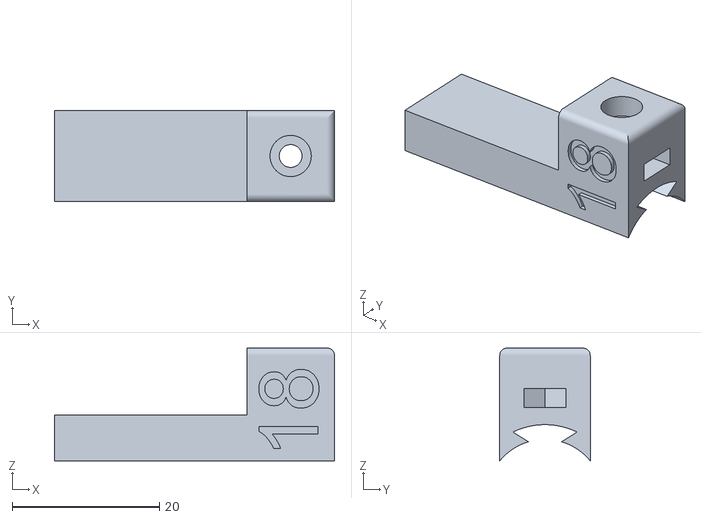
[picture p87: CAD file, 2024-11-09]
bow_4/fingerSlider18.stl
38.0 x 12.3 x 15.3
