reivaxy/celloAid/bow_3/thumb/circles/thumbRing17.stl

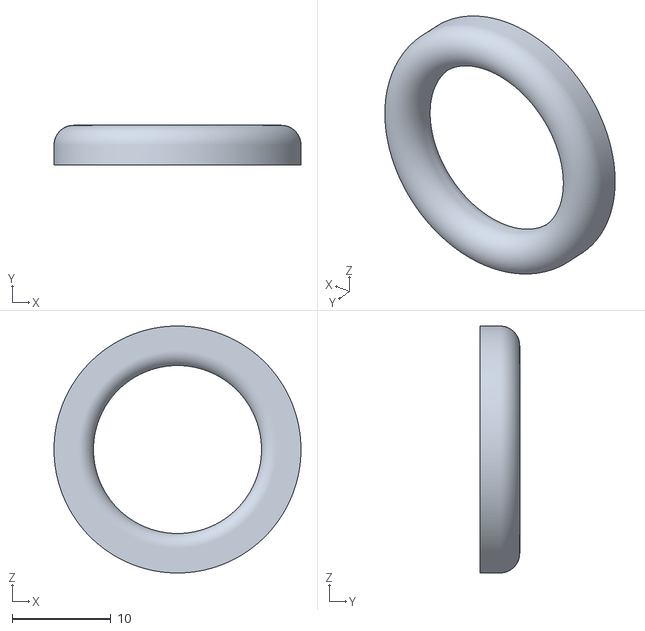
[picture p88: CAD file, 2024-08-30]
bow_3/thumb/circles/thumbRing17.stl
25.0 x 4.00 x 25.0
