reivaxy/celloAid/bow_3/thumb/thumbSlider14.3mf

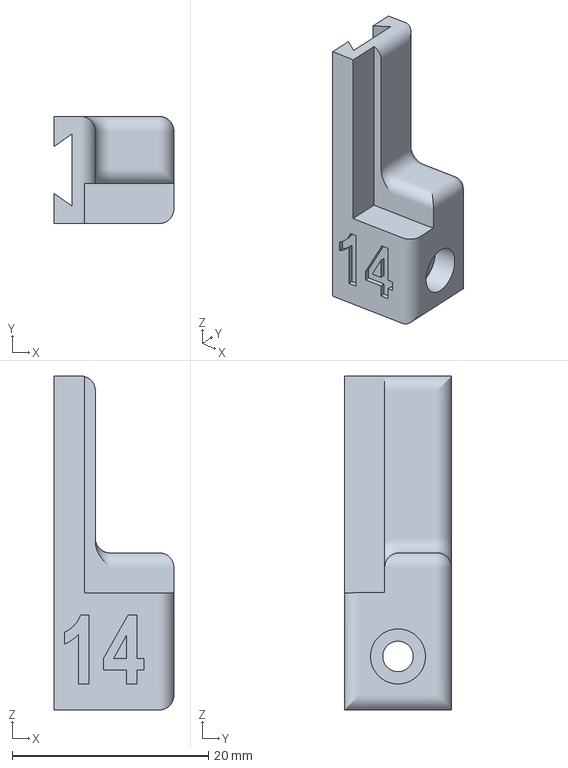
[picture p89: CAD file, 2024-10-21]
bow_3/thumb/thumbSlider14.3mf
12.2 x 10.9 x 34.0 mm
