reivaxy/celloAid/bow_3/thumb/circles/thumbRing15.stl

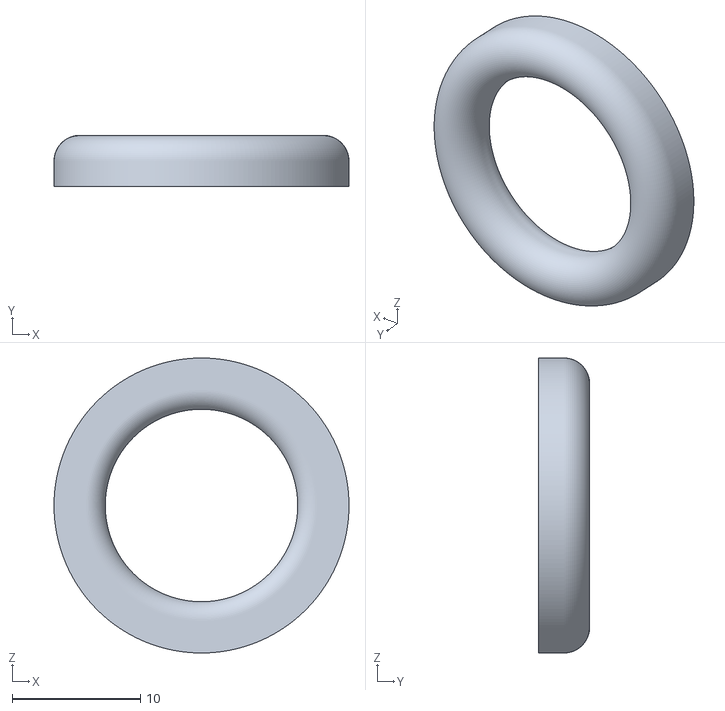
[picture p90: CAD file, 2024-08-30]
bow_3/thumb/circles/thumbRing15.stl
23.0 x 4.00 x 23.0
