reivaxy/celloAid/bow_3/thumb/thumbRing18.3mf

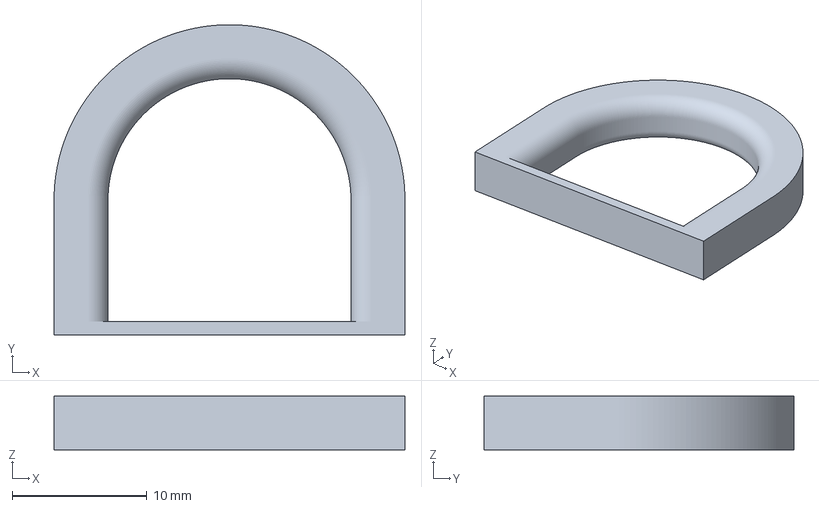
[picture p91: CAD file, 2024-10-21]
bow_3/thumb/thumbRing18.3mf
26.0 x 23.0 x 4.00 mm
