reivaxy/celloAid/bow_3/thumb/circles/thumbRing21.stl

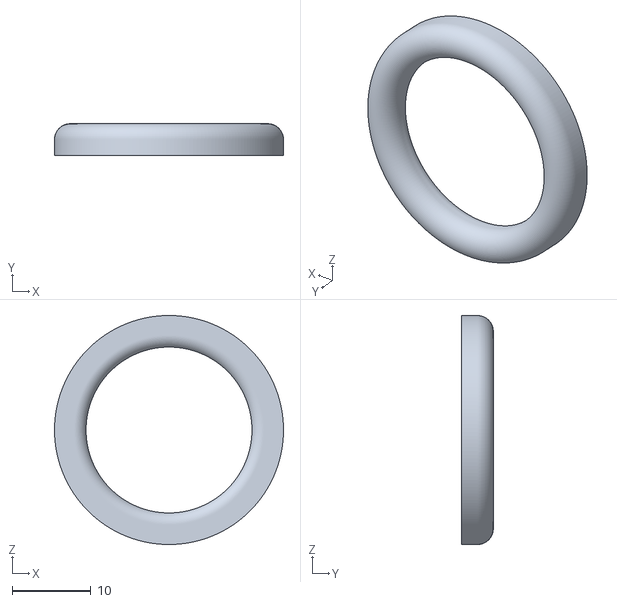
[picture p92: CAD file, 2024-08-30]
bow_3/thumb/circles/thumbRing21.stl
29.0 x 4.00 x 29.0
