reivaxy/celloAid/bow_3/thumb/thumbSlider17.3mf

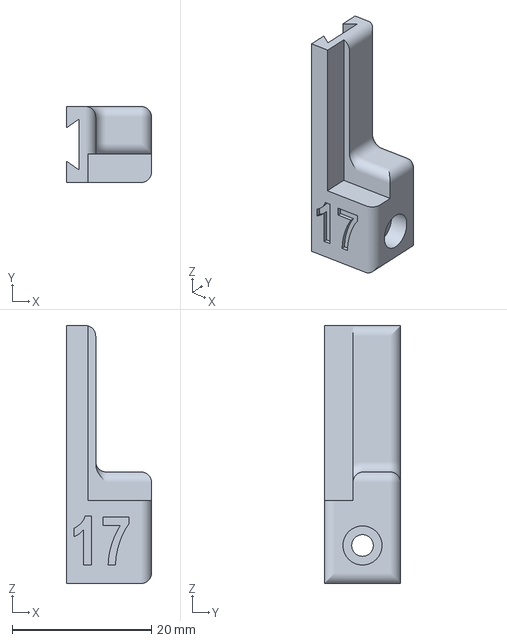
[picture p93: CAD file, 2024-10-21]
bow_3/thumb/thumbSlider17.3mf
12.2 x 10.9 x 37.0 mm
