reivaxy/celloAid/bow_3/thumb/circles/thumbRing20.stl

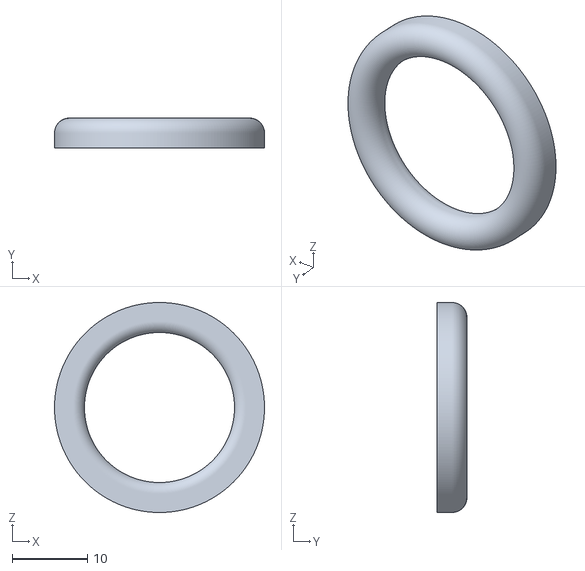
[picture p94: CAD file, 2024-08-30]
bow_3/thumb/circles/thumbRing20.stl
28.0 x 4.00 x 28.0
