reivaxy/celloAid/bow_3/thumb/thumbSlider21.3mf

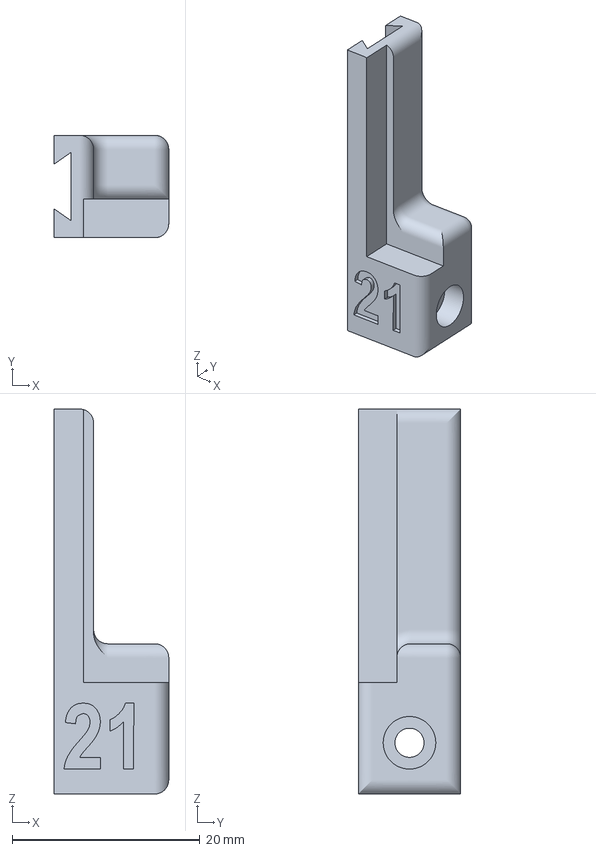
[picture p95: CAD file, 2024-10-21]
bow_3/thumb/thumbSlider21.3mf
12.2 x 10.9 x 41.0 mm
