reivaxy/celloAid/bow_3/thumb/circles/thumbRing16.stl

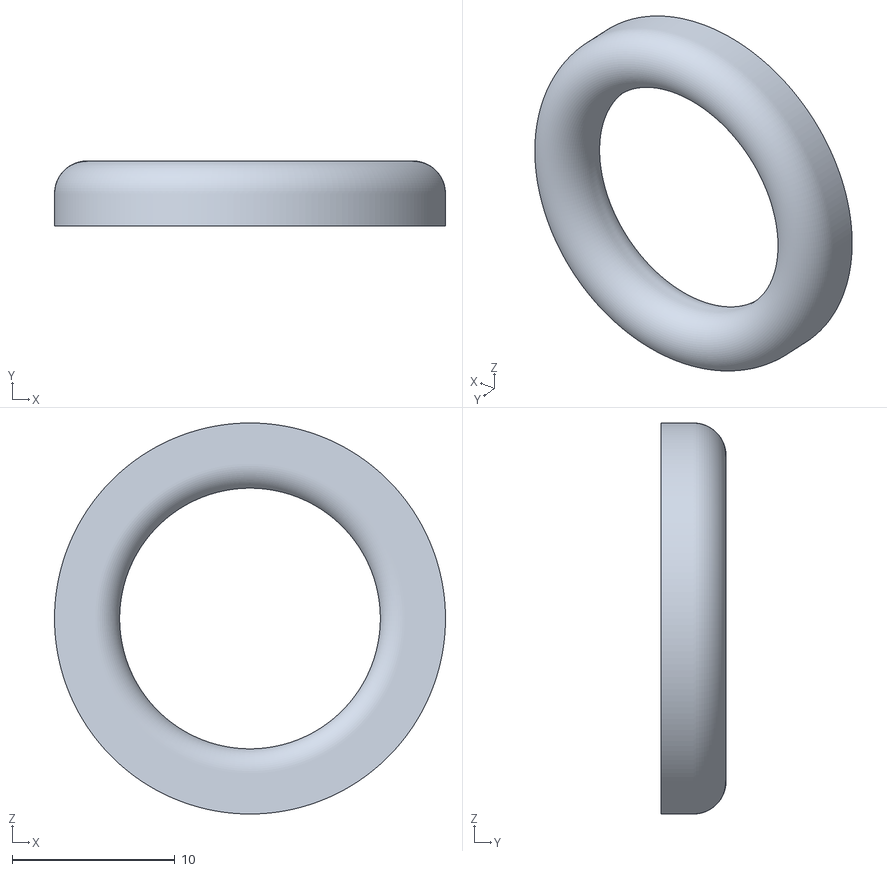
[picture p96: CAD file, 2024-08-30]
bow_3/thumb/circles/thumbRing16.stl
24.0 x 4.00 x 24.0
